0x616c6f6e/esp32s31-mp3/mechanical/connector-layout/README.md

# H1 马达 / H2 电池线束方案

打开 `Q2_Connector_Layout.FCStd`。本装配使用当前 `hardware-q2-placement` 的实际元件 STEP，结合保存的 E 版外壳，增加马达、候选托座及五根导线通道。外壳仍为 50 × 80 × 13.5 mm，主板仍为 46 × 76 mm；没有增加 PCB 走线。E 版原文件保留。

默认视图隐藏 LCD、操作小板、其螺钉和后盖，电池半透明，以便查看内部线束；可在对象树恢复显示。`connector-plan.png` 是带说明的位置图，`assembly-isometric.png` 和 `assembly-top.png` 为 FreeCAD 装配预览。

## 连接器与位置

| 位号 | 板端 / 线端 | KiCad 坐标、角度、板面 | 外壳坐标 |
| --- | --- | --- | --- |
| H1 马达 | JST BM02B-ACHSS-GAN-ETF / ACHR-02V-S | (130, 113) mm，−90°，F.Cu | (19, 64) mm |
| H2 电池 | JST BM03B-ACHSS-GAN-ETF / ACHR-03V-S | (142, 109) mm，−90°，F.Cu | (7, 60) mm |

两者均为 1.2 mm 间距、顶部插合、侧面出线的 ACH 端子，标称插合高度 1.4 mm。1～3 芯规格在 AWG28 条件下额定 2 A。H1 靠近 U11 马达驱动区，线束从电池下方绕到其右侧的马达；H2 位于电池左边缘附近，通过过孔连接背面的充电/电量计电路。两座沿外壳 +X 出线，插装顺序为先插线束，再安放电池和操作小板；装好电池后不能直接向上拔插 H1。

| 接口 | 1 脚 | 2 脚 | 3 脚 |
| --- | --- | --- | --- |
| H1 | MOTOR_OUT_N | MOTOR_OUT_P | — |
| H2 | VBAT | BAT_TS | GBAT |

H1 的两根线都是差分驱动输出，不是电源正负线。H2 的 GBAT 是电池负端，经电流检测电阻接系统地，布线时不能旁路检测电阻。针序按 PCB 焊盘编号核对，不能凭预制线颜色判断；电池线束必须按本项目顺序压接。两芯/三芯壳避免接口互插。

电池线建议 AWG28、绝缘外径不超过 0.63 mm，压接端子 SACH-003G-P0.2。马达原配 AWG32 线需使用 SACH-003G-P0.2B，并核对绝缘外径在 0.38～0.50 mm 范围；不符合时应换用匹配线材/线束。线束模型只是通道，不是生产线长和折弯图。

来源：[JST ACH 官方规格](https://www.jst-mfg.com/product/pdf/eng/eACH.pdf)。KiCad 标准库提供本版焊盘封装；3D 使用项目自建的保守插合包络，不是厂商精细 CAD，生成脚本在 `../../hardware-q2-placement/scripts/build_ach_models.py`。

## 推荐马达

候选 **Precision Microdrives C08-005 圆形 LRA**，与现有 DRV2605L 驱动方式匹配。数据表修订 004 的尺寸为直径 8 ± 0.1 mm、厚度 3.3 ± 0.15 mm，额定 1.8 Vrms、235 Hz。不能把官网旧摘要中的 3.2 mm 当作最大厚度。样机需按装配质量校准 DRV2605L 的 LRA 模式和驱动电压；这是候选选型，尚未完成实物振感验证。

马达中心外壳坐标 **(39, 57) mm**，底面 Z=7.1 mm；位于电池右侧、操作小板下方，与天线和屏幕排线区域分开。按直径 8.1 × 厚度 3.45 mm 最大包络检查，与操作小板间隙 0.55 mm，与电池预留包络间隙 2.65 mm。侧壁托座为候选结构，内径 8.3 mm、外径 9.2 mm，底板 Z=6.7～7.0 mm，预留 0.1 mm 胶层和出线槽；强度、材料、加工公差待打样。托座与外壳侧壁的接触是设计连接。

来源：[C08-005 官方数据表](https://www.precisionmicrodrives.com/datasheets/C08-005%20-%20datasheet-004.pdf)。该数据表标为采样目标规格，采购前向厂商确认供货版本。

## 电池建议与选型边界

推荐方向是 **单节 3.7 V、4.2 V 满充的高倍率软包，带保护板和独立 NTC 引线**。优先向厂商询价 252030 / 302030 尺寸级的定制成品包；型号数字只是电芯尺寸线索，不能作为成品装配尺寸承诺。当前未找到同时有可核实尺寸、电流和三线定义的现成型号，因此没有在 BOM 中虚填具体电池料号或容量。

现有电池预留空间为外壳 (8.3, 37, 7.8) mm 起的 **24 × 34 × 3 mm** 包络。建议向电池厂提出以下采购目标：

- 成品包平面最大 22 × 32 mm，含保护板、胶带和极耳折边；让厂家给出初始厚度、循环后最大厚度及膨胀余量，确认都能被现有高度空间接受。必要时重新调整内部叠层，不能强压软包。
- 初步电流筛选目标为持续至少 0.6 A、脉冲至少 1 A / 100 ms；这些是待整机测量校核的需求目标，不是已经验证的电池性能或整机功耗。容量按厂商可实现方案确认。
- 线从电池上短边靠左处引出，三线按 H2 针序压接；电池负端与 NTC 公共端的连接方式必须与电路匹配。
- NTC 优先按现有 BQ25895 的温度检测网络匹配，不能只看“10 kΩ”就认定可互换；核对 B 值、温度曲线及保护阈值。当前 R10 标为 `0R/NC`，需在确定电池后明确装配为 0 Ω，并结合 R13=5.23 kΩ、R14=30.1 kΩ 校核；本次没有宣称温度保护已经验证。
- 确定电池后再设置 BQ25895 充电电流、终止电流和充电电压，不能直接沿用大容量电池的参数。

例如 [Honcell HCP302030NZC 150 mAh 成品数据表](https://www.honcell.com/Public/Uploads/uploadfile/files/20240409/DATASHEETHCP302030NZC3.7V150mAhPACK2024EDRE01.pdf)给出的持续放电电流仅 150 mA，不满足上述初步筛选目标，所以本方案没有把它作为可直接采购的推荐件。

## 检查与使用

`fit-check.json` 记录新增马达最大包络、托座、导线与 122 个元件以及外壳/电池/操作小板/排线的实体相交检查。排线插接、线材最小弯曲半径、装配工具空间、电池寿命膨胀和完整公差链尚未验证。

KiCad 当前 DRC 0 违规、0 原理图一致性问题，386 条未连接符合未布线状态。原 555 个焊盘的身份及网络保留，新增 4 个无网络机械固定焊盘。原理图仅修改 H1/H2 的值、封装、资料和供应商字段；连接器图形仍使用原通用针脚图形以保持所有接线位置不变。

`../../hardware-q2-placement/scripts/build_harness_assembly.py` 可由 FreeCAD 重建本规划装配；将覆盖本目录生成结果，不会改写 E 版外壳。该文件是布局与结构讨论模型，尚不是可直接投产的外壳或线束图纸。
