0x616c6f6e/esp32s31-mp3/mechanical/enclosure-q2/README.md

# Q2 外观修订 B 与 2.09 英寸屏幕模型

本版取代旧 A 版作为外观方向：采用 Q2 的大圆角机身、上部横向圆角黑色屏窗、下部黑色操作环和中心电源键，正面不露螺丝。旧 `../enclosure/` 保留用于追溯。**本版是外观和屏幕结构原型，现有 KiCad PCB 尚不能直接装入，不能作为整机生产定版。**

## 打开文件

- `ESP32S31_MP3_Q2_B.FCStd`：原生 FreeCAD 外壳工程，`Parameters` 表驱动盒体、开孔、屏幕和操作环的原生布尔特征。默认显示整机外观。
- `LCD209_36x43.FCStd`：独立屏幕工程，包含背光外形、LCD 玻璃、显示区、展开排线和 21 个端部触点。
- `exports/q2-front.png`、`q2-assembled.png`、`q2-exploded.png`：正面、立体和爆炸图。
- `exports/lcd-dimensions.svg` / `.png`：屏幕尺寸图；`lcd209-flat-reference.step` 为带展开排线的模型，`lcd209-module-only.step` 为模组外形。
- `exports/q2-*.step` / `.stl`：外壳、后盖、操作环面片和中心键四个样件。STL 仅供外观/结构打样，不代表装机兼容。树脂材料和收缩补偿仍须按打印工艺选择；1.2 mm 壁厚不是已验证的 FDM 工艺规格。
- `exports/pcb-target-envelope-NOT-ROUTED.step`：47 × 76、R10.5 的新 PCB 轮廓建议实体，**不是新 KiCad 布线文件**。

## 外观和尺寸

主体为 50 × 80 × 13.5 mm，另加屏幕保护盖板后最大厚度 14.2 mm，与所查 Q2 标称外包络一致。主体平面 R12、边缘滚圆 0.55、盖板 46 × 40 × 0.6 / R10.5、操作环直径 33、中心键直径 11.4 mm 均为依据实物照片比例拟合的设计值，不是厂家机械图数据，不能声称精确复刻。

官方说明书第 12 页确认：中心键控制电源/亮灭屏；上方返回，左右切歌，下方播放暂停；圆环为音量触摸环。本版保留该外观与预留空间。当前主板没有完整的操作环电路，需另外设计电容感应环和按键板；中心开关可按既有设计需求连接 KEY/GND，但开关型号、行程、固定方式尚待选型。黑色环面片应采用可透电容感应的非金属材料。

本项目现有硬件只有 3.5 mm 耳机口和 USB-C，不包含 Q2 的 4.4 mm 平衡口；开孔按现有电路接口数量设计。TF 开孔也按现有卡座位置布置，因此接口布局不是 Q2 的逐孔复制。后盖两颗 M1.6 螺钉从背面装入，1.3 mm 导孔与头部空间为打样设计值。

## 屏幕尺寸的依据

| 项目 | 用户图纸 / 本版采用值 |
|---|---|
| BL 外形 | 36.33 ±0.1 × 43.45 ±0.1 mm |
| LCM 总厚 | 1.46 ±0.1 mm |
| LCD 玻璃 | 36.13 × 43.25 mm |
| A.A. 显示区 | 34.18 × 40.05 mm，顶部内缩 1.05 mm |
| 安装方向 | 模组旋转 90°，43.45 横向、36.33 纵向 |
| FPC 从模组边缘展开长度 | 46.14 ±0.5 mm |
| FPC 尾宽 / 触点中心跨度 | 6.6 ±0.05 / 6 ±0.03 mm |
| 间距 / 露铜长度 | 0.3 ±0.03 / 2.5 ±0.3 mm |
| 显示规格 | 2.09 英寸 IPS，320 RGB × 375，QSPI，驱动 IC 9855 |
| 触摸层 | 资料标注“无”，模型不将其视为触摸模组 |
| 资料连接器 | OK-F302-21115，与 PCB 现有封装尚未核对兼容性 |

图纸右侧 A.A. 内缩 1.08 mm 与按名义宽度居中得到的 1.075 mm 存在 0.005 mm 四舍五入差。本版以 A.A. 宽度和居中为准，不把该差异误作公差。

**估算项**：模组 R10、A.A. R9；FPC 宽颈 18 × 12.8、膜厚 0.12、折弯中性层 R0.8、触点宽 0.18 / 铜厚 0.015 mm。宽颈的实际过渡曲线、补强片、触点面朝向和引脚 1 方向未获得完整标注。玻璃/背光厚度拆分 0.30/1.16 只作示意，保证模组总厚 1.46。图示黑色单面胶 0.03 mm 是否已计入 LCM 总厚待供应商确认，未擅自把总厚增加至 1.49。

外加保护盖板和 0.18 mm 周边胶框是本设计的额外部件，不是用户屏幕资料中的 TP。排线折叠模型保持 46.14 mm 的中性线长度，含半圆弯折长度 πR；它是空间研究，不是经过供应商批准的弯折方案。折叠端部位于机身坐标 x≈3.10 mm，**未与原 FPC2 实际插接**。折弯模型是几何快照，修改 FPC 参数后须重新构建。

## 现有 PCB 的实际冲突

检查用的是当前 KiCad 导出的板体及 A 版器件包络，板体位置 x=1、y=1、名义后铜面 z=7.1 mm；坐标 +Y 朝底部接口，+Z 朝屏幕。器件 XY 来自封装，器件高度仍是估算。

- 现有 48 × 76 / R1.2 PCB 与大圆角壳体相交体积 **90.001504 mm³**。需要修改板角、边缘布局及固定孔，不能靠扩大壳体解决后继续称为 Q2 尺寸。
- 保守器件包络检查涉及 **U9、H1、C5、C58、CN1**。详见 `exports/validation.json`；U9 和 H1 为主要相交项。现有 PCB 和器件的相交实体已存为红色可视对象，预览为 `pcb-conflict-review.png`。
- 屏幕移到上方后，金属背光区域在 XY 上覆盖现有 U9 天线区域。需重新安排主控/天线与屏幕的位置，不能把三维不碰撞等同于射频合格。
- FPC2 连接器、操作环感应板、中心开关、电池与新固定结构尚须联合调整。新壳的螺钉柱也可能占用原板区域；新的板框建议仅作为空间约束，未完成网络重布线。

## 验证与再生成

`exports/validation.json` 记录零件实体有效性、外包络、已建模外壳/屏幕/排线间的几何相交量，以及旧板冲突。`external_geometry_pass=true` 只表示所列外形零件检查通过；**`pcb_fits=false`** 明确表示当前 PCB 不适配。

`exports/export-verification.json` 记录四个样件 STEP 重导入为有效单实体、STL 封闭、屏幕 STEP 外形尺寸复核，以及原生参数改变后重算/恢复。未验证真实器件公差、胶粘强度、开关寿命、防水、射频或量产装配。

参数来源是 `parameters.json`。FreeCAD 内的 `Parameters` 支持编辑原生特征；对于排线折叠、参考几何、图标和爆炸图这些快照，需要修改 JSON 后重建才同步。运行 `Rebuild.FCMacro` 前保存并关闭本目录的两个文档；脚本不覆盖旧 A 版和 KiCad 文件。重建会恢复 JSON 中的值，因此应把希望保留的表格修改同步回 JSON。

PCB/器件/电池参考形状已冻结在 `reference/source-*.brep`，来源哈希见 `reference/source-manifest.json`。PCB 或布局数据改变后，构建脚本会要求先刷新参考形状，避免用旧形状生成看似最新的干涉报告。尺寸 SVG/PNG 由 `draw_dimensions.py` 生成；调整 JSON 后需用安装了 Pillow 的 Python 重跑该脚本。

## 参考来源

- 用户提供屏幕图和参数表保存在 `reference/lcd-dimensions.png`、`lcd-specifications.png`。
- [山灵 Q2 官方说明书](http://openwin.shanling.com:9000/pdf/sms/Q2v1.0.pdf)，本地 `reference/Q2v1.0.pdf`，第 4 / 12 页用于操作件布局。
- [Q2 商品实物照片与尺寸规格](https://www.e-earphon.com/collections/new_item/products/778580)，核对正面上部横屏、下部圆环和整机 80 × 50 × 13.5 / 含屏 14.2 mm。照片仅作观察参考，未作为项目素材复制。
