0x616c6f6e/esp32s31-mp3/hardware-controls/mechanical/controls-and-keycaps.png

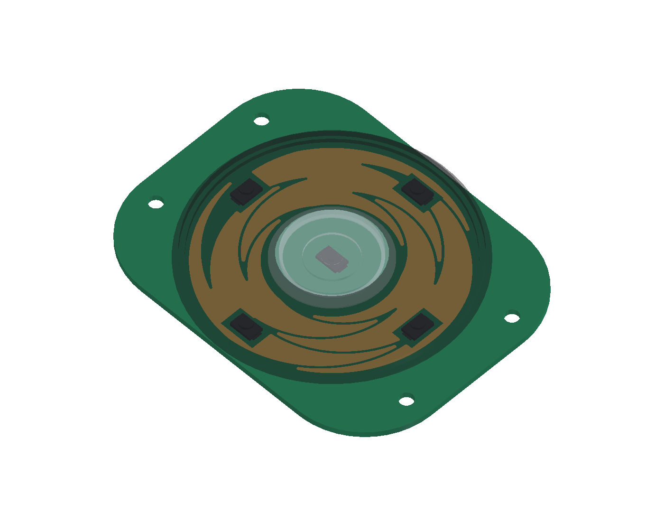
hardware-controls/mechanical/controls-and-keycaps.png
