0x616c6f6e/esp32s31-mp3/hardware-controls/mechanical/exterior.png

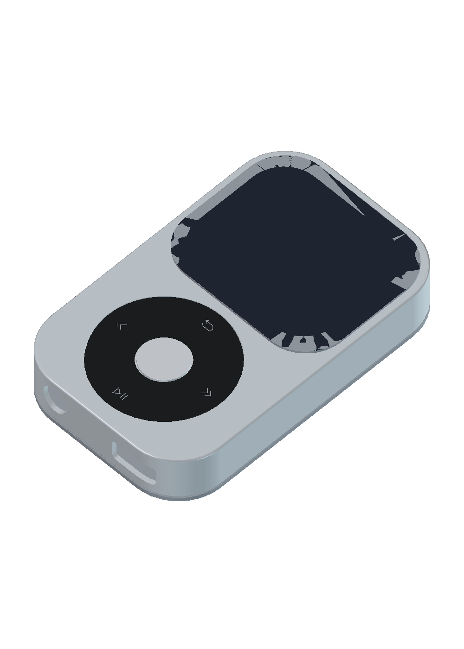
hardware-controls/mechanical/exterior.png
