0x616c6f6e/esp32s31-mp3/hardware-controls/mechanical/ffc-section.png

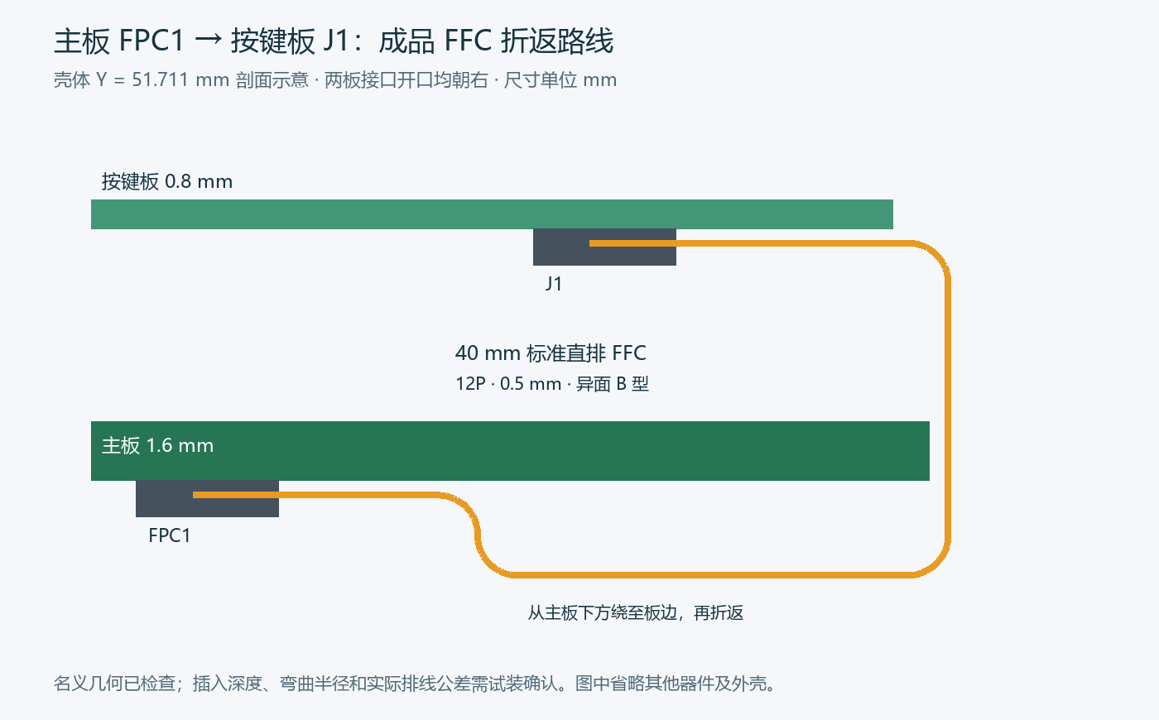
hardware-controls/mechanical/ffc-section.png
