0x616c6f6e/esp32s31-mp3/hardware-controls/output/3d-back.png

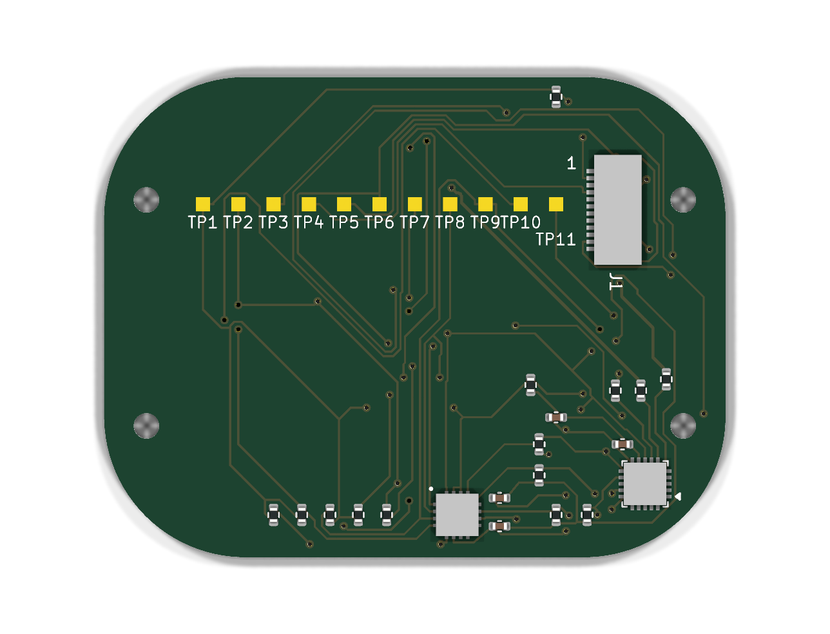
hardware-controls/output/3d-back.png
