0x616c6f6e/esp32s31-mp3/hardware-controls/output/ch32v006-review/back.png

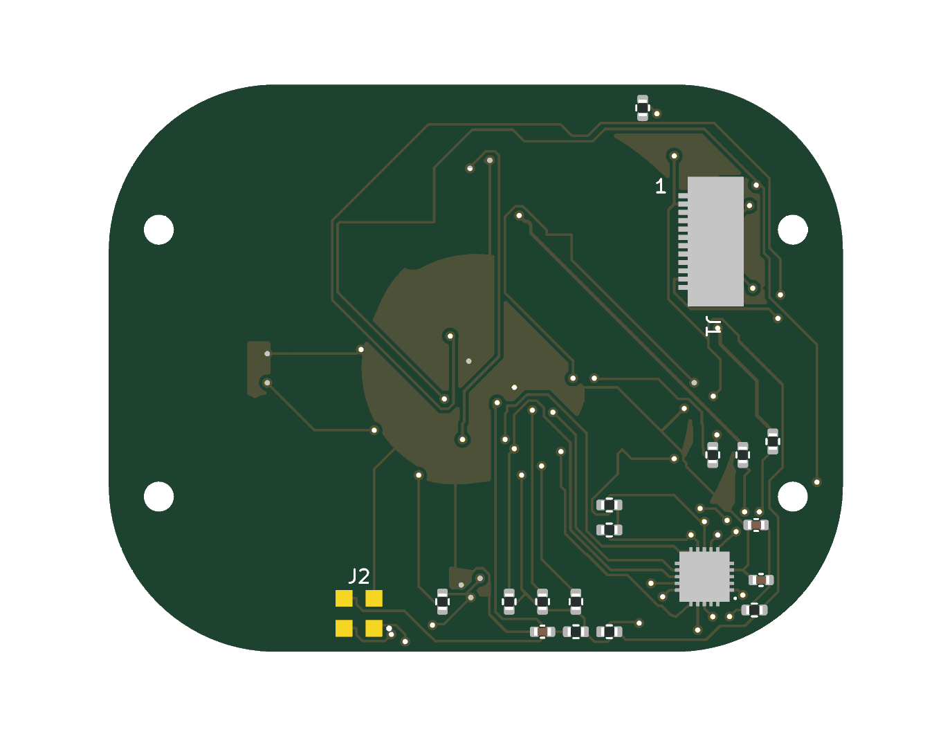
hardware-controls/output/ch32v006-review/back.png
