0x616c6f6e/esp32s31-mp3/hardware-controls/output/controls-overview.png

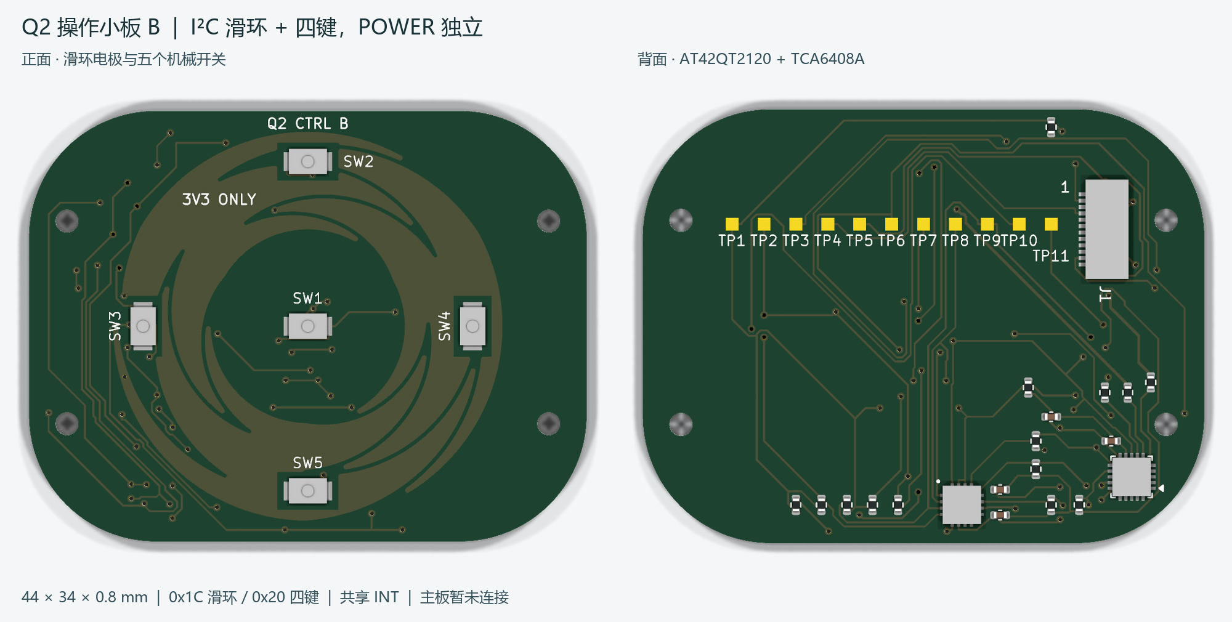
hardware-controls/output/controls-overview.png
