0x616c6f6e/esp32s31-mp3/hardware-controls/output/schematic.png

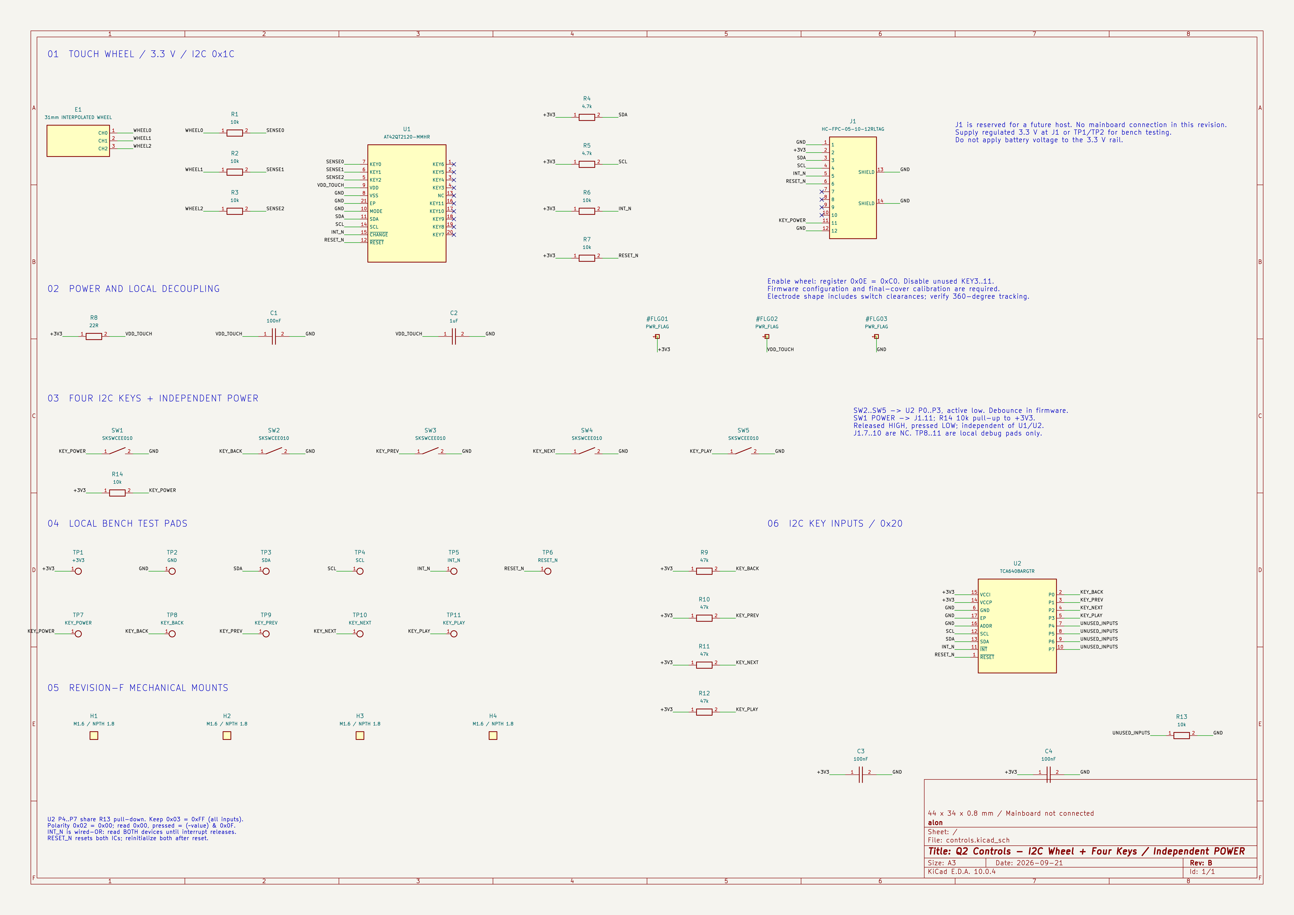
hardware-controls/output/schematic.png
