0x616c6f6e/esp32s31-mp3/hardware-display-adapter/am213-fpc-adapter/output/routing-obstacles.png

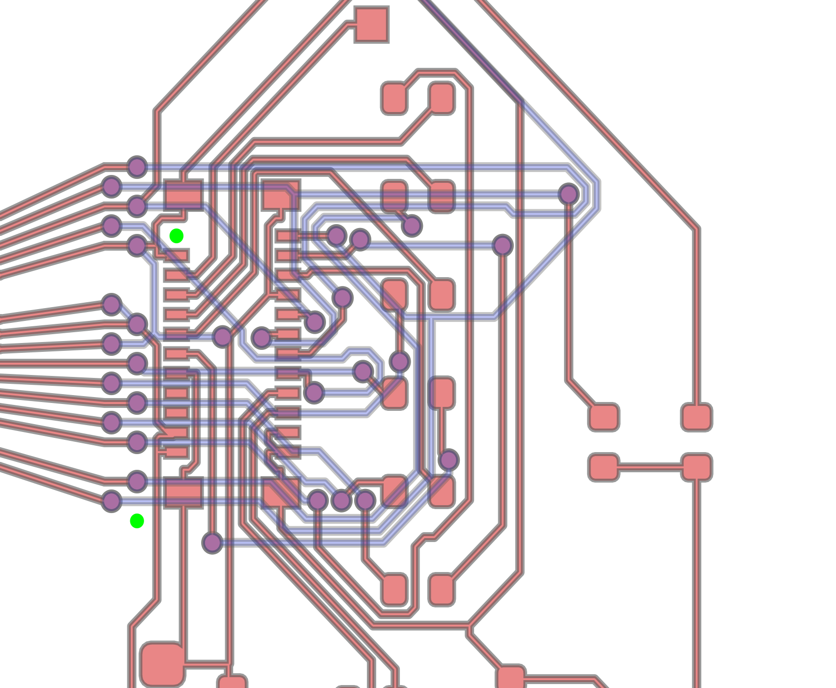
hardware-display-adapter/am213-fpc-adapter/output/routing-obstacles.png
