0x616c6f6e/esp32s31-mp3/hardware-display-adapter/am213-fpc-adapter/output/schematic/am213-fpc-adapter.png

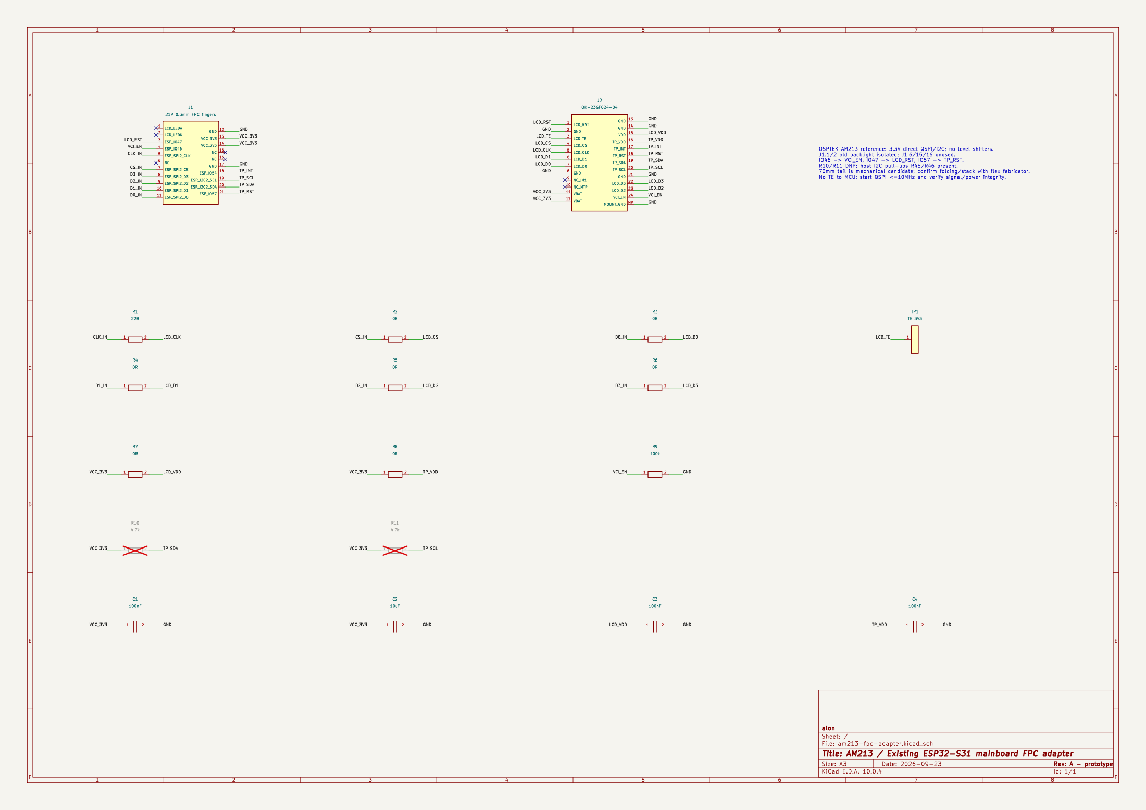
hardware-display-adapter/am213-fpc-adapter/output/schematic/am213-fpc-adapter.png
