0x616c6f6e/esp32s31-mp3/hardware-display-adapter/fpc-layout-concept.png

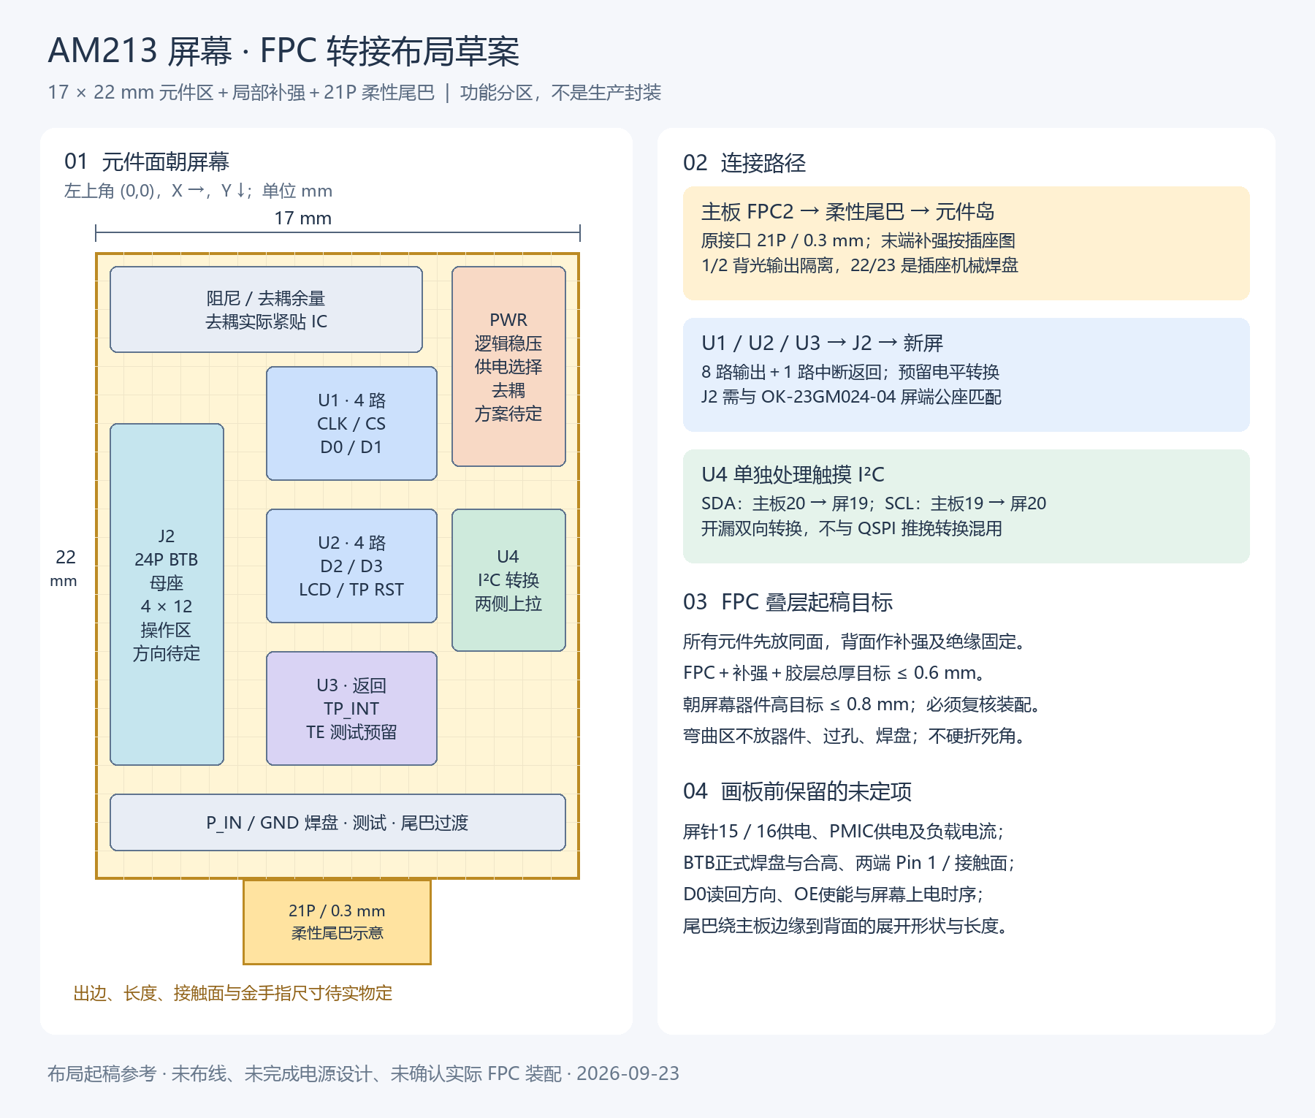
hardware-display-adapter/fpc-layout-concept.png
