0x616c6f6e/esp32s31-mp3/hardware-display-adapter/reference/1-241226143025125.png

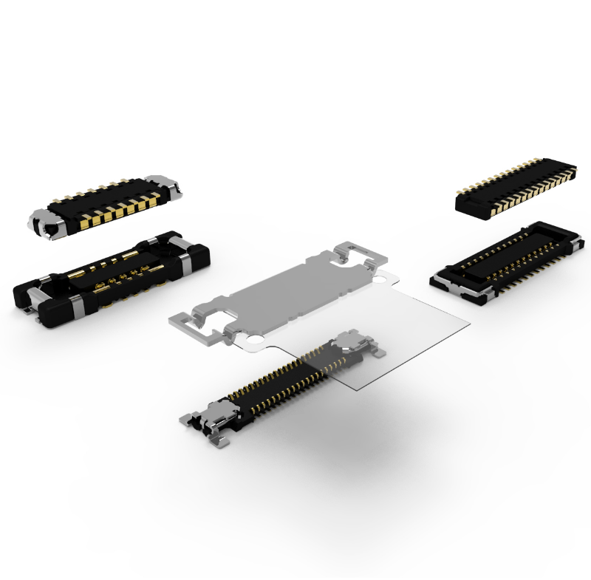
hardware-display-adapter/reference/1-241226143025125.png
