0x616c6f6e/esp32s31-mp3/hardware-q2-v2-plan/placement-overview.png

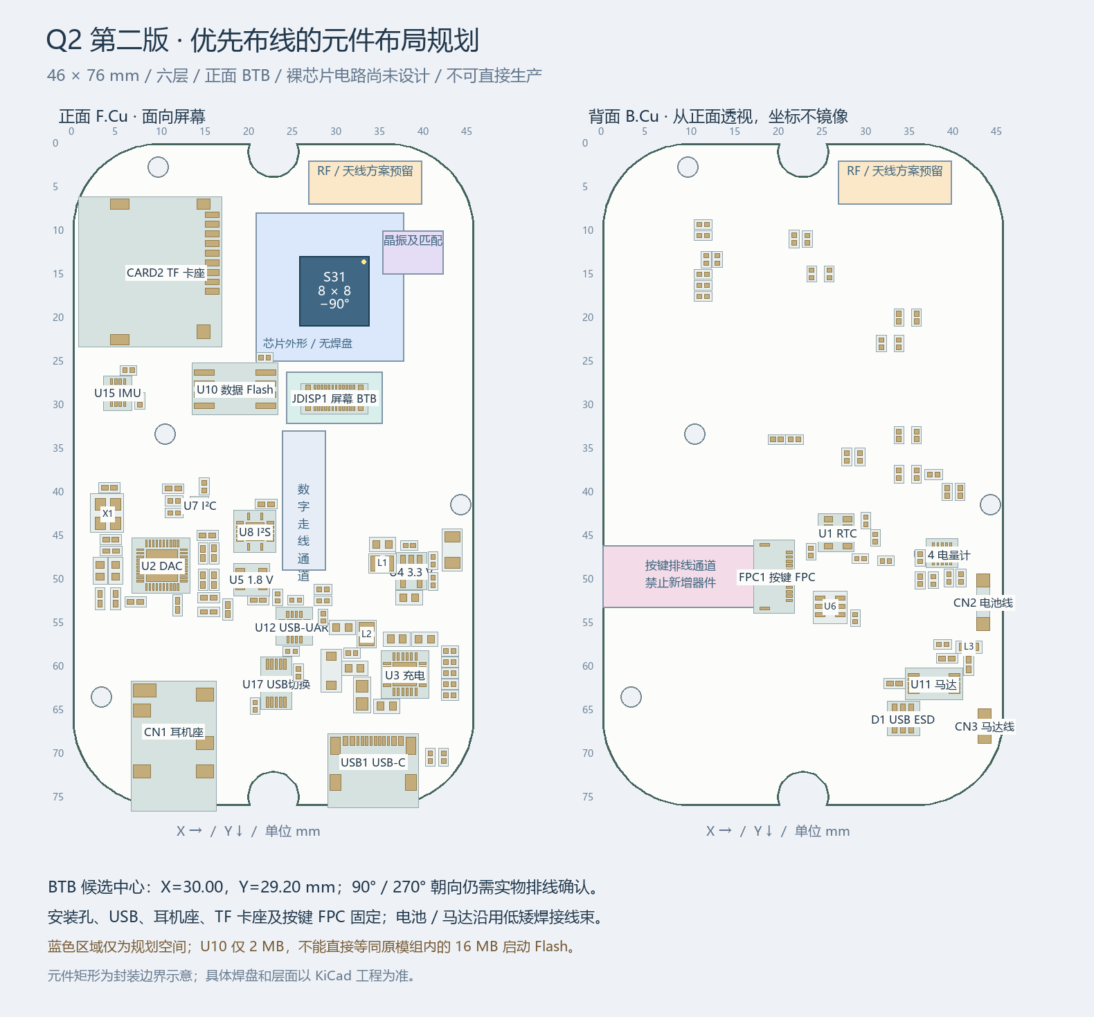
hardware-q2-v2-plan/placement-overview.png
