0x616c6f6e/esp32s31-mp3/hardware-q2-v2/output/pcb-overview.png

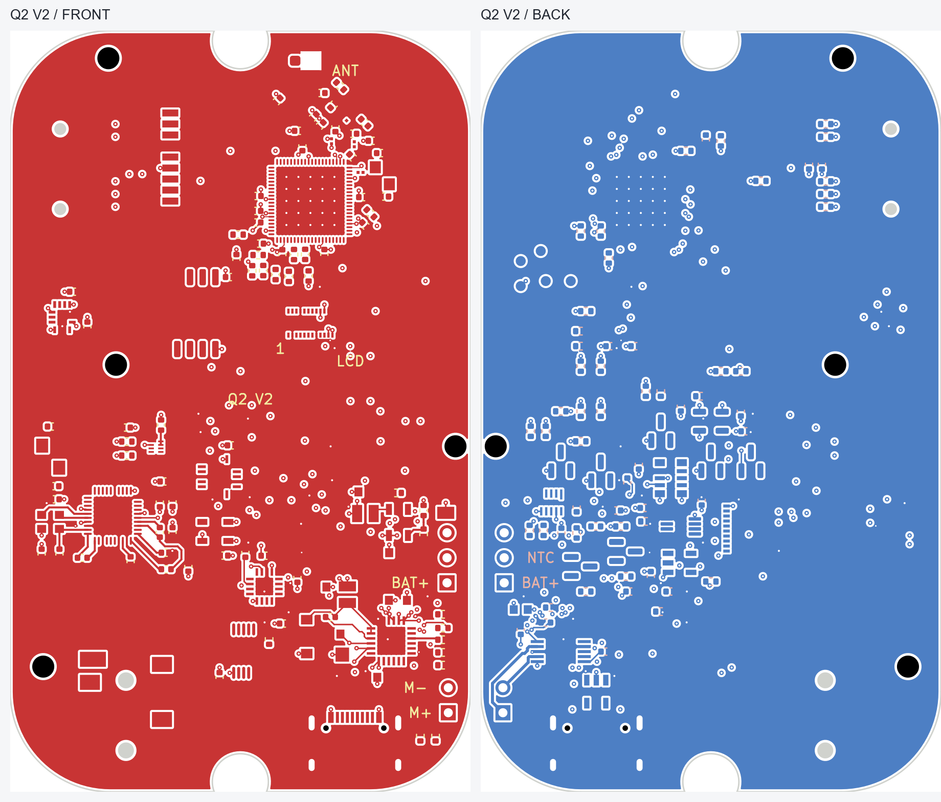
hardware-q2-v2/output/pcb-overview.png
