0x616c6f6e/esp32s31-mp3/mechanical/connector-layout/connector-plan.png

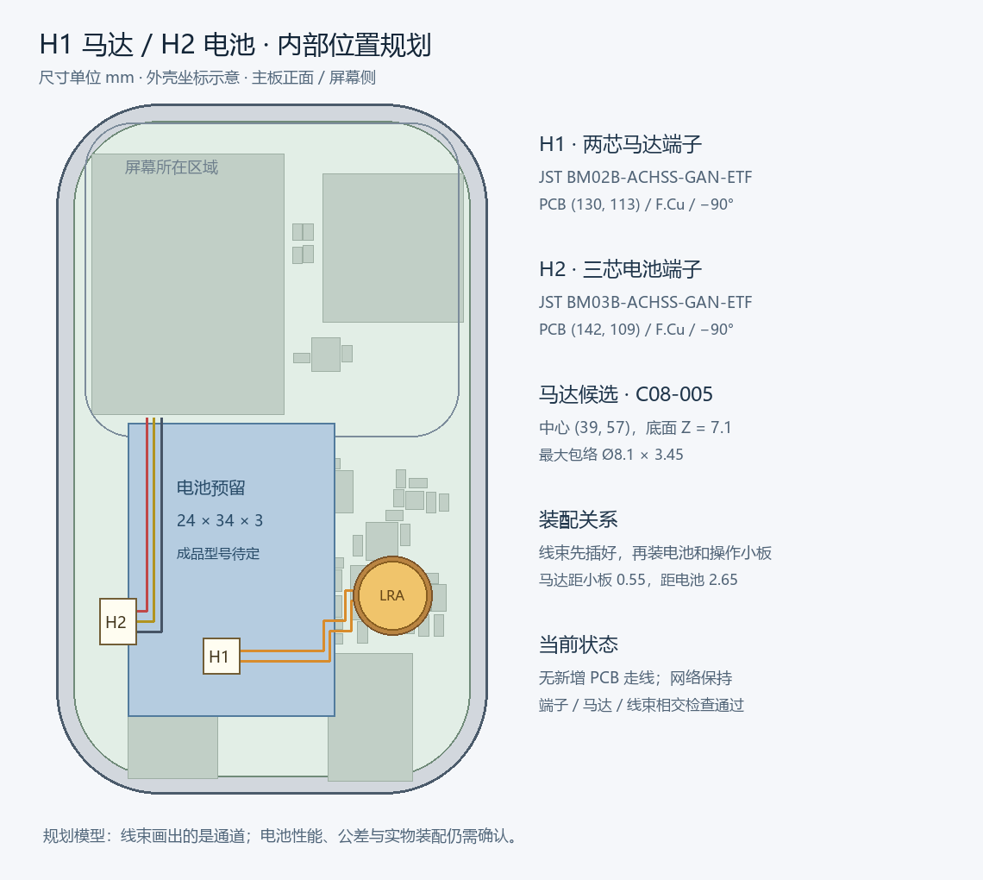
mechanical/connector-layout/connector-plan.png
