0x616c6f6e/esp32s31-mp3/mechanical/display-fit/exports/current-fit-rear-isometric.png

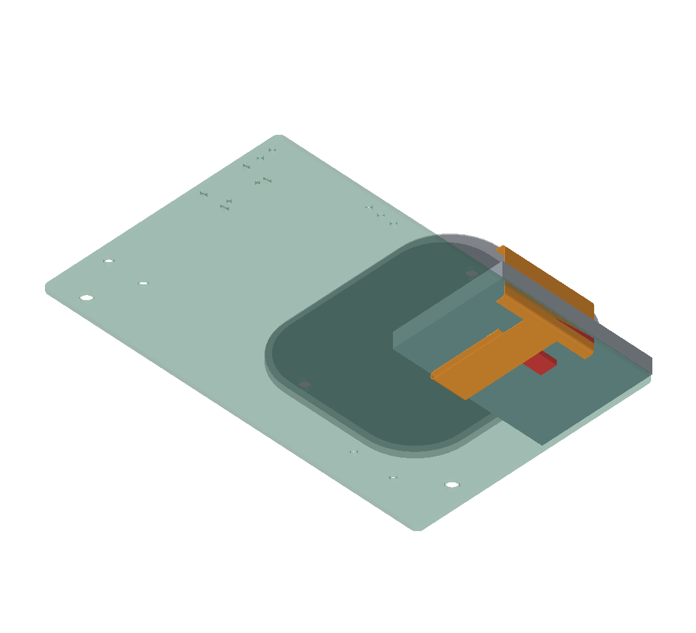
mechanical/display-fit/exports/current-fit-rear-isometric.png
