0x616c6f6e/esp32s31-mp3/mechanical/display-fit/exports/display-fit-review.png

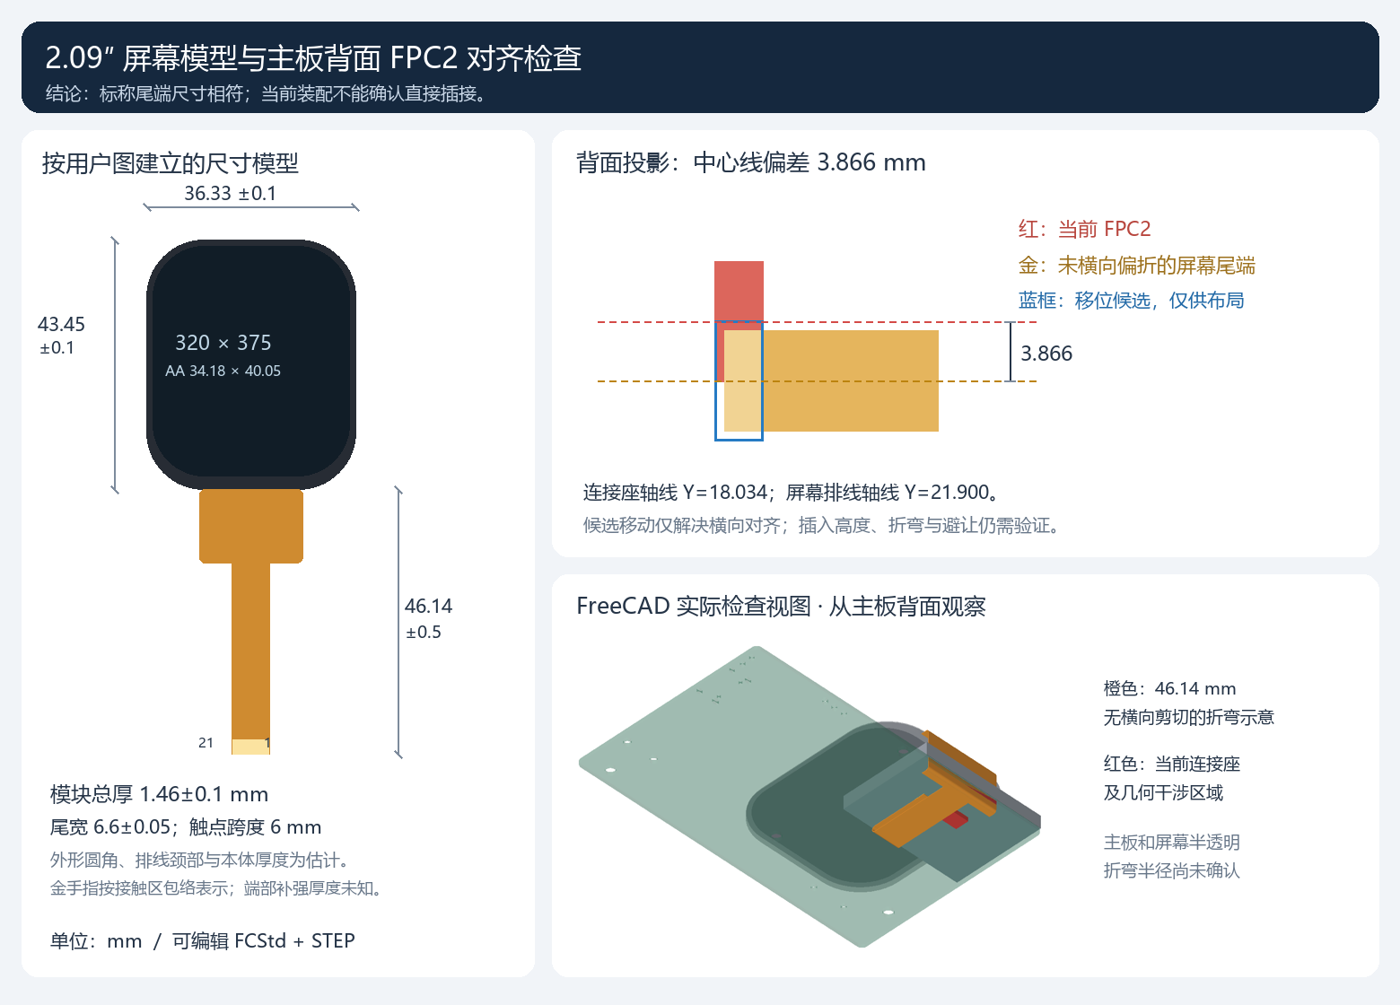
mechanical/display-fit/exports/display-fit-review.png
