0x616c6f6e/esp32s31-mp3/mechanical/display-fit/exports/lcd-native-isometric.png

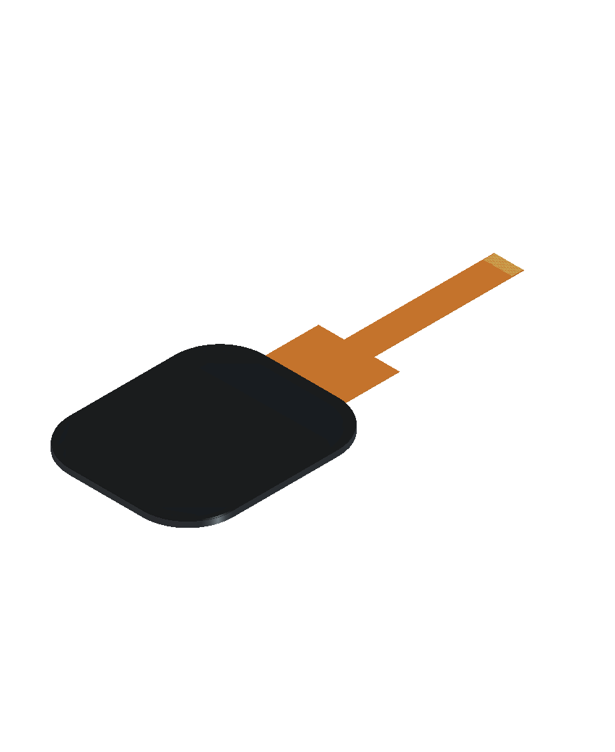
mechanical/display-fit/exports/lcd-native-isometric.png
