0x616c6f6e/esp32s31-mp3/mechanical/display-fit/reference/connector-drawing.png

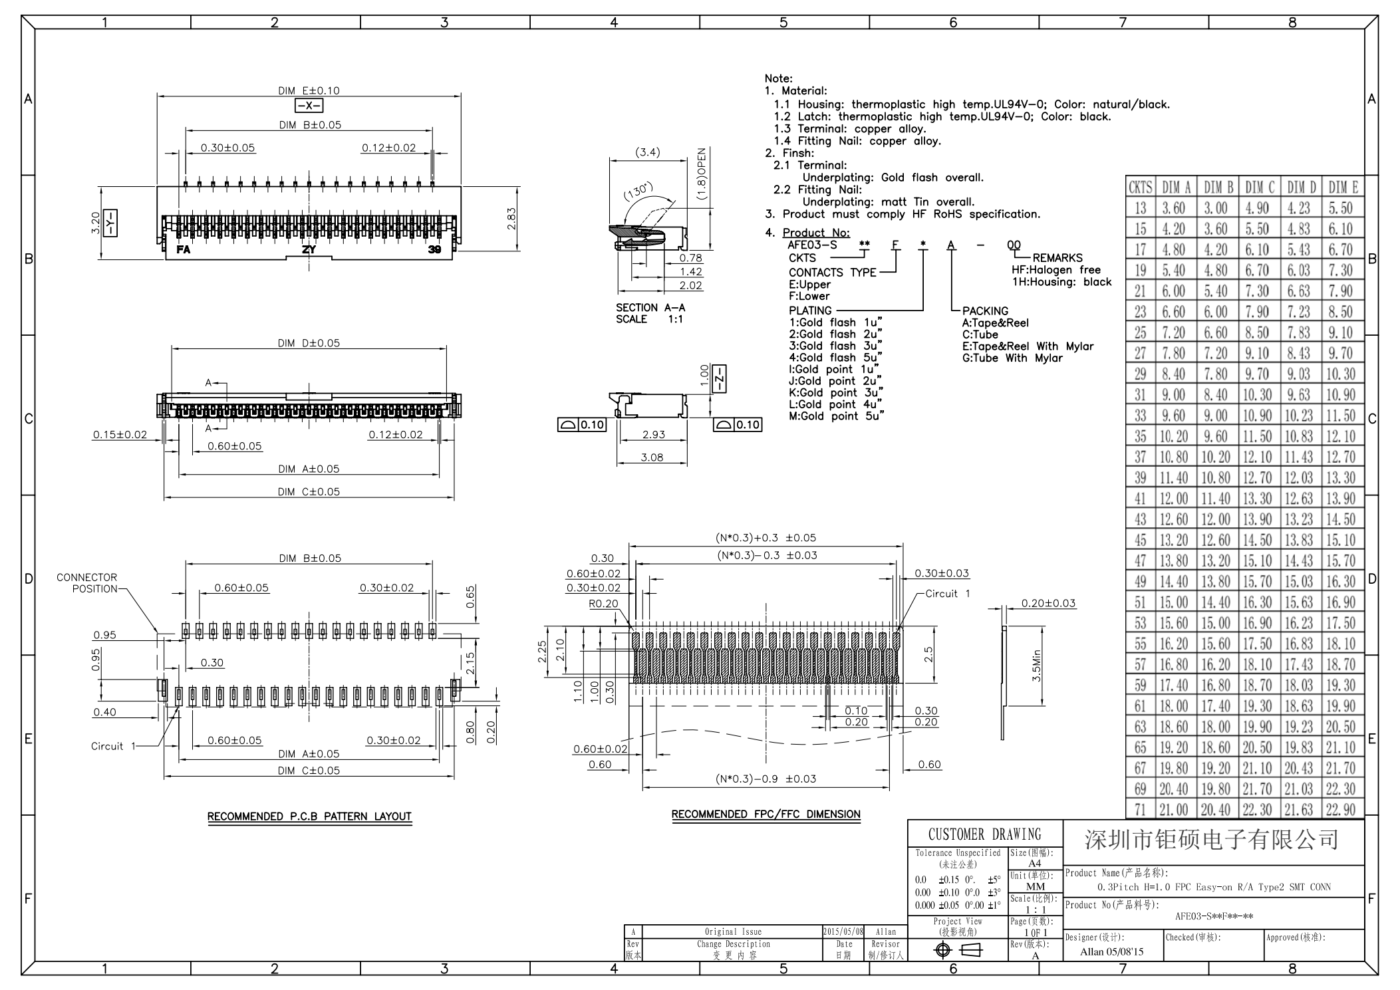
mechanical/display-fit/reference/connector-drawing.png
