0x616c6f6e/esp32s31-mp3/mechanical/display-fit/reference/lcd-specifications.png

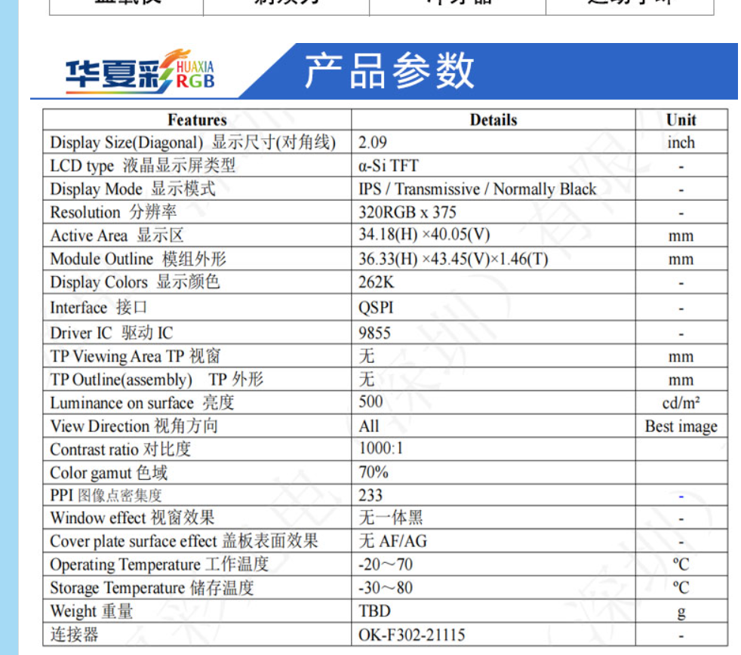
mechanical/display-fit/reference/lcd-specifications.png
