0x616c6f6e/esp32s31-mp3/mechanical/enclosure-final-g/back-internals.png

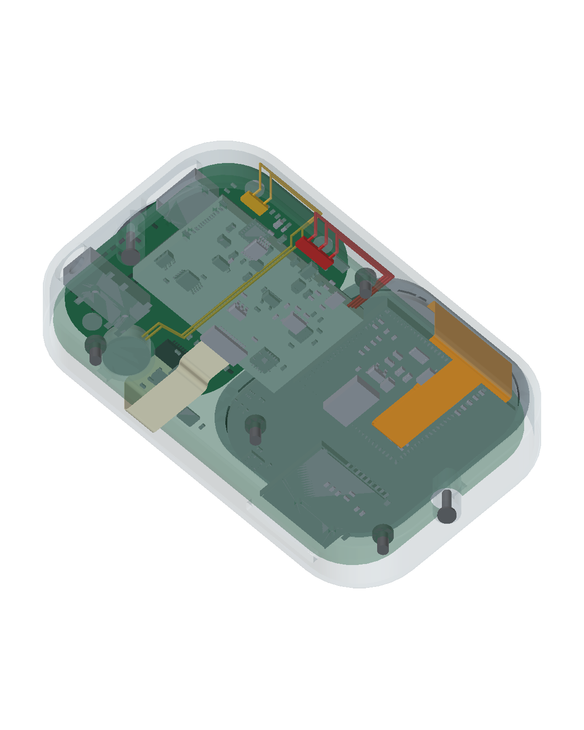
mechanical/enclosure-final-g/back-internals.png
