0x616c6f6e/esp32s31-mp3/mechanical/enclosure-final-g/reference/CN3.pdf.png

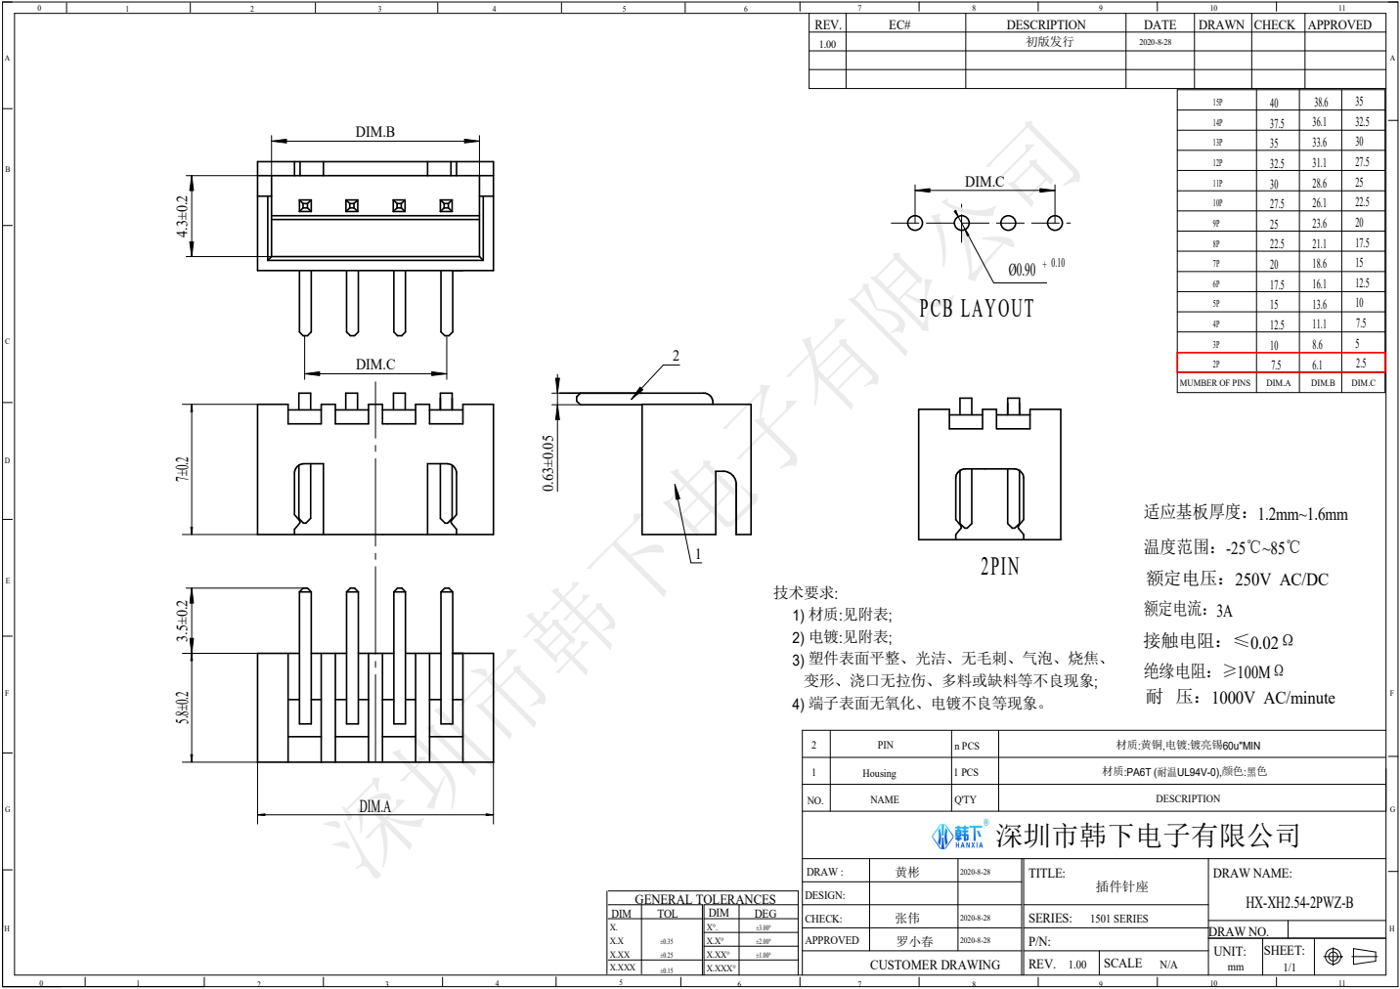
mechanical/enclosure-final-g/reference/CN3.pdf.png
