0x616c6f6e/esp32s31-mp3/mechanical/enclosure-final-h/reinforced-upper-shell.png

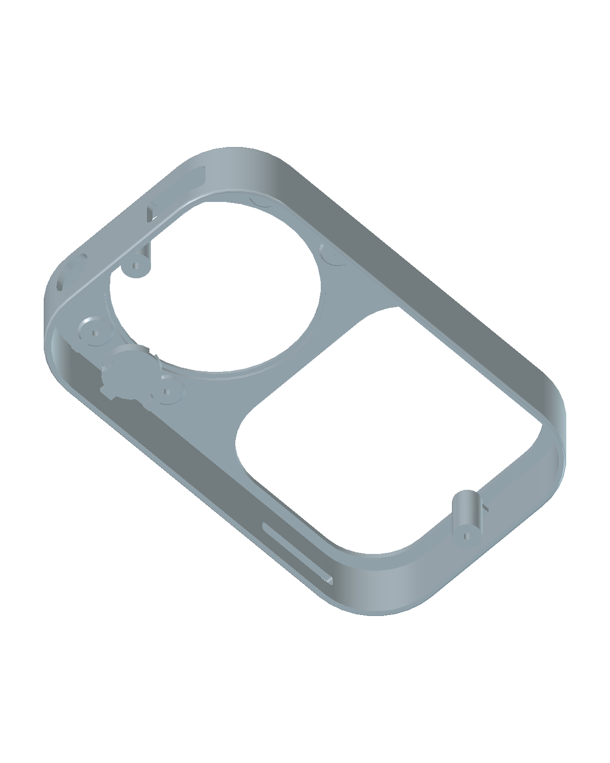
mechanical/enclosure-final-h/reinforced-upper-shell.png
