0x616c6f6e/esp32s31-mp3/mechanical/enclosure-final-j/controls-mount-view.png

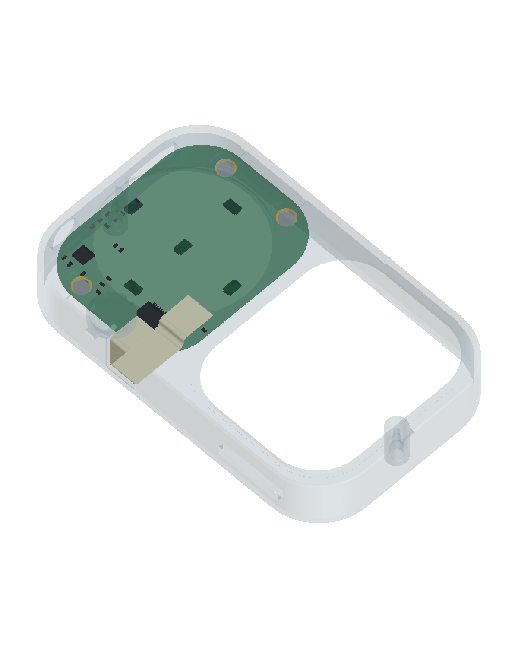
mechanical/enclosure-final-j/controls-mount-view.png
