0x616c6f6e/esp32s31-mp3/mechanical/enclosure-final-j/insert-section.png

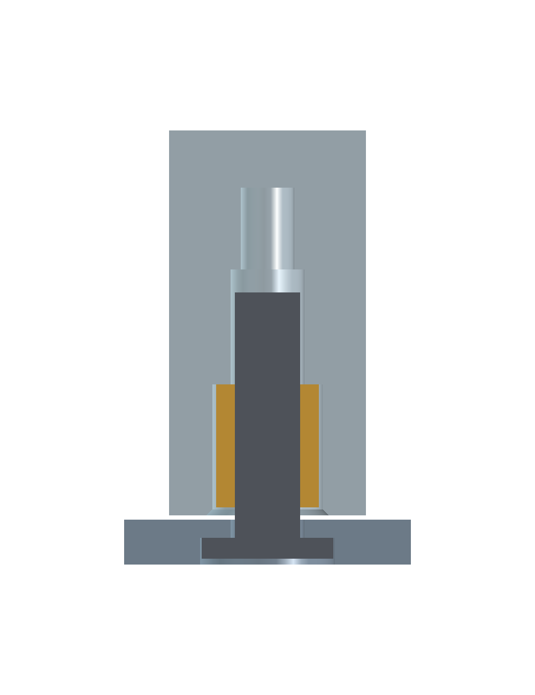
mechanical/enclosure-final-j/insert-section.png
