0x616c6f6e/esp32s31-mp3/mechanical/enclosure-q2/exports/q2-exploded.png

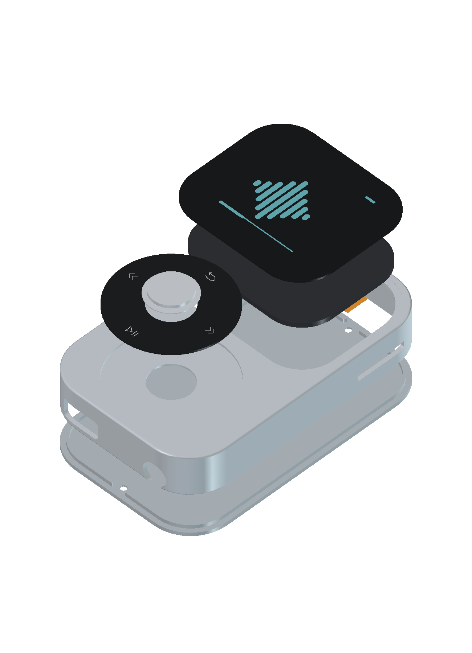
mechanical/enclosure-q2/exports/q2-exploded.png
