0x616c6f6e/esp32s31-mp3/mechanical/enclosure/exports/exploded.png

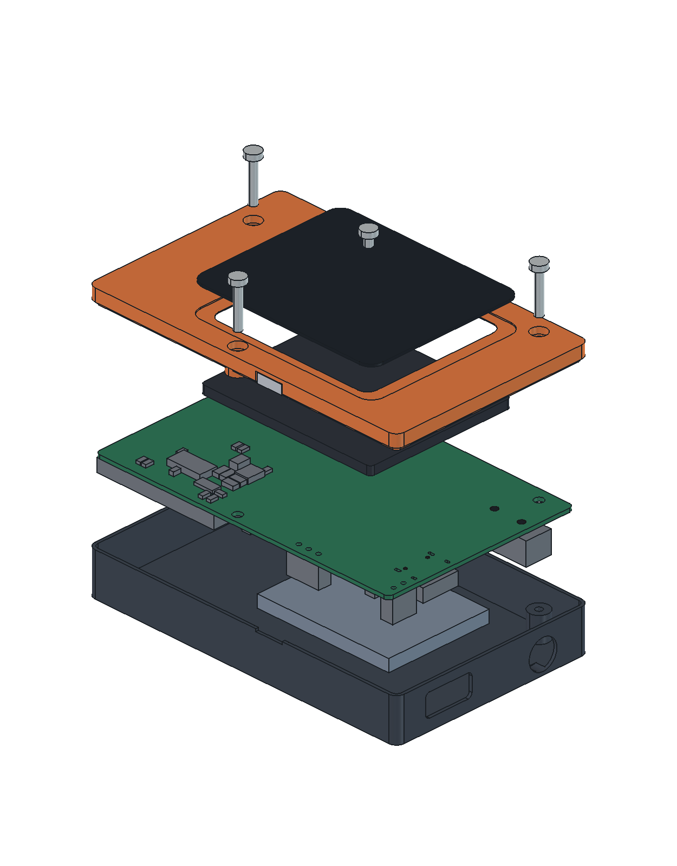
mechanical/enclosure/exports/exploded.png
