0x616c6f6e/esp32s31-mp3/mechanical/final-board-review/motor-jack-conflict.png

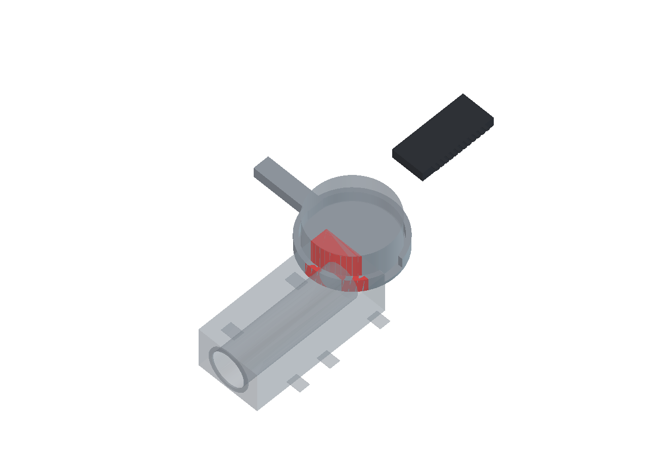
mechanical/final-board-review/motor-jack-conflict.png
