0x616c6f6e/esp32s31-mp3/mechanical/v2-btb-placement/placement-top.png

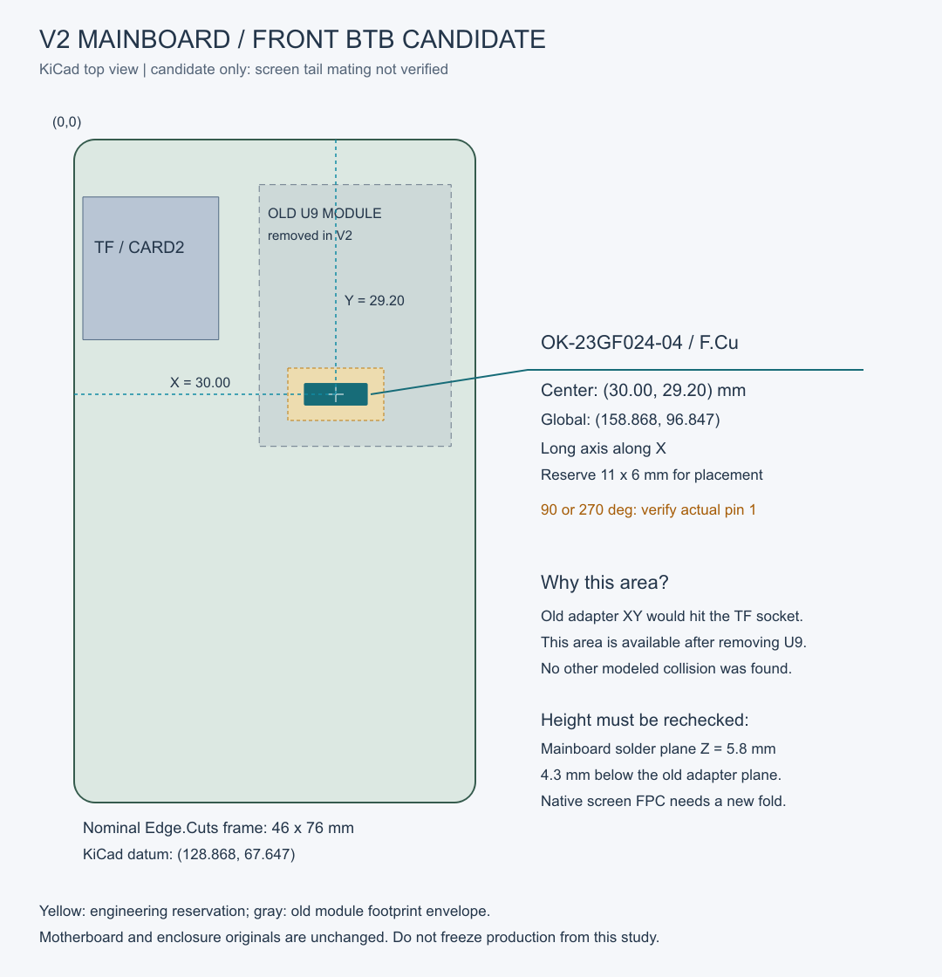
mechanical/v2-btb-placement/placement-top.png
