0x616c6f6e/esp32s31-mp3/mechanical/enclosure-q2-d/exports/mainboard-target-envelope-NOT-ROUTED.step

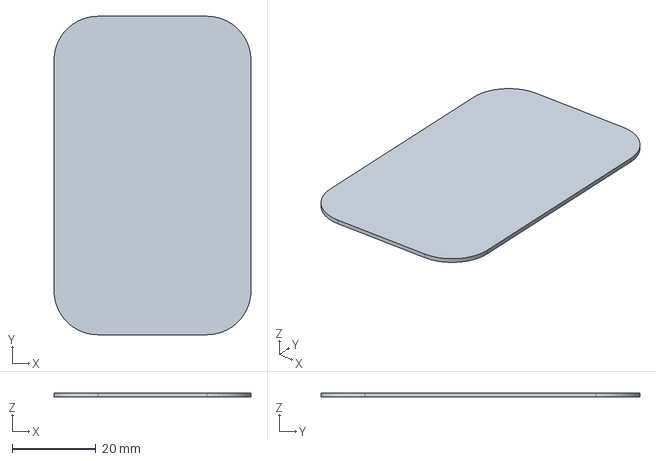
[picture p83: CAD file, 2026-09-21]
mechanical/enclosure-q2-d/exports/mainboard-target-envelope-NOT-ROUTED.step
47.0 x 76.0 x 1.00 mm
