0x616c6f6e/esp32s31-mp3/mechanical/enclosure-q2/exports/q2-appearance-assembly.step

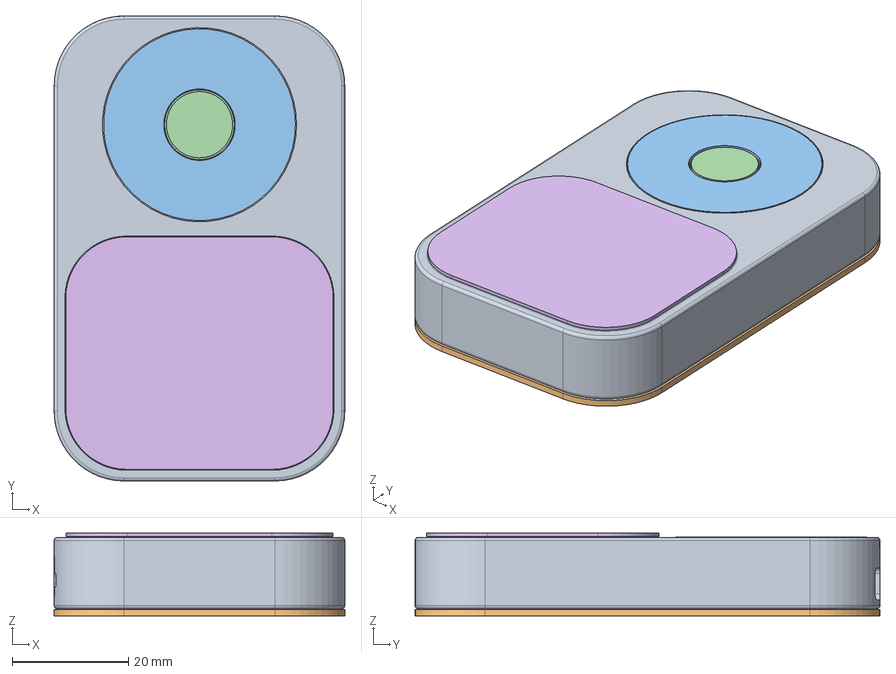
[picture p84: CAD file, 2026-09-21]
mechanical/enclosure-q2/exports/q2-appearance-assembly.step
50.0 x 80.0 x 14.2 mm
