0x616c6f6e/esp32s31-mp3/mechanical/enclosure-q2-f/exports/assembly-F-current-PCB.step

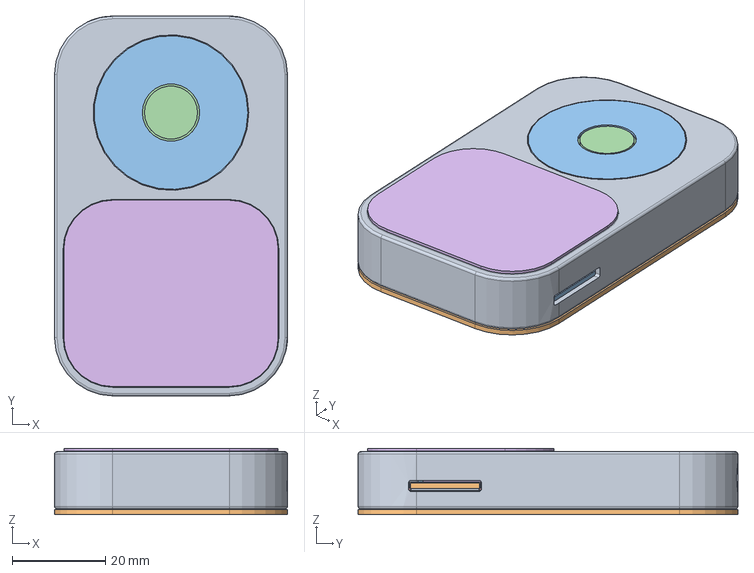
[picture p85: CAD file, 2026-09-21]
mechanical/enclosure-q2-f/exports/assembly-F-current-PCB.step
50.0 x 81.5 x 14.2 mm
