0x616c6f6e/esp32s31-mp3/hardware-controls/models3d/FH19C_12.step

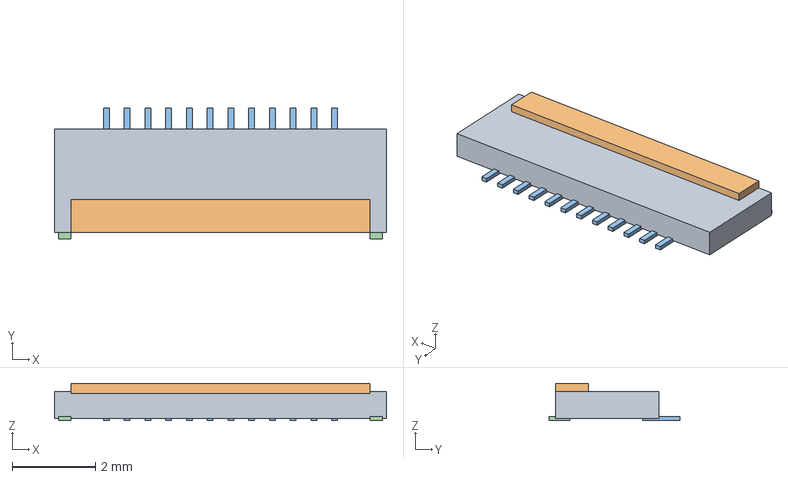
[picture p86: CAD file, 2026-09-24]
hardware-controls/models3d/FH19C_12.step
8.00 x 3.15 x 0.9 mm
FH19C_12_0
FH19C_12_1
FH19C_12_2
FH19C_12_3
FH19C_12_4
FH19C_12_5
FH19C_12_6
FH19C_12_7
FH19C_12_8
FH19C_12_9
FH19C_12_10
FH19C_12_11
FH19C_12_12
FH19C_12_13
FH19C_12_14
FH19C_12_15
