0x616c6f6e/esp32s31-mp3/hardware-controls/output/ch32v006-review/candidate/models3d/CH32V006_QFN20.step

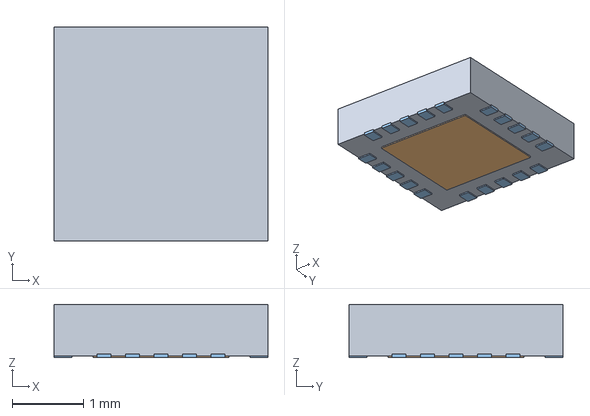
[picture p87: CAD file, 2026-09-24]
hardware-controls/output/ch32v006-review/candidate/models3d/CH32V006_QFN20.step
3.00 x 3.00 x 0.75 mm
