0x616c6f6e/esp32s31-mp3/hardware-controls/output/controls-ch32v006.step

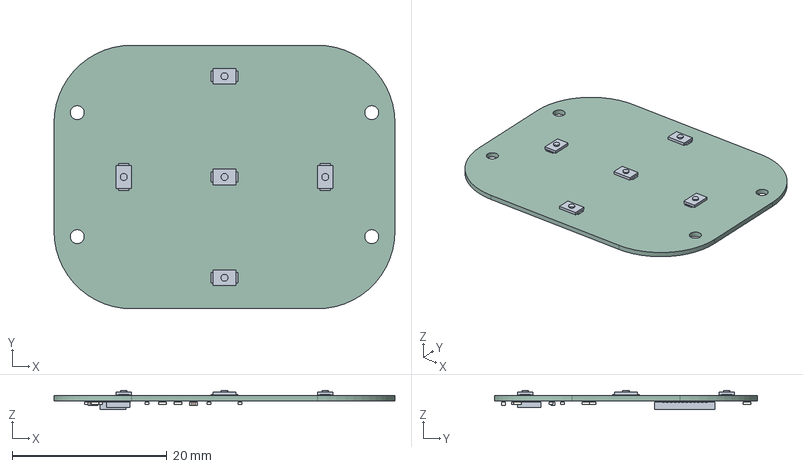
[picture p88: CAD file, 2026-09-24]
hardware-controls/output/controls-ch32v006.step
44.0 x 34.0 x 2.48 mm
SKSW_3x2_0 x 5
SKSW_3x2_1 x 5
SKSW_3x2_2 x 5
SKSW_3x2_3 x 5
C_0402_1005Metric x 3
R_0402_1005Metric x 13
Housing
Latch
Pin1
Pin2
Pin3
Pin4
Pin5
Pin6
Pin7
Pin8
Pin9
Pin10
Pin11
Pin12
Mount
Mount001
controls_PCB
