0x616c6f6e/esp32s31-mp3/hardware-display-adapter/am213-fpc-adapter/models3d/Q2_L_BTB_Fit_Review.FCStd

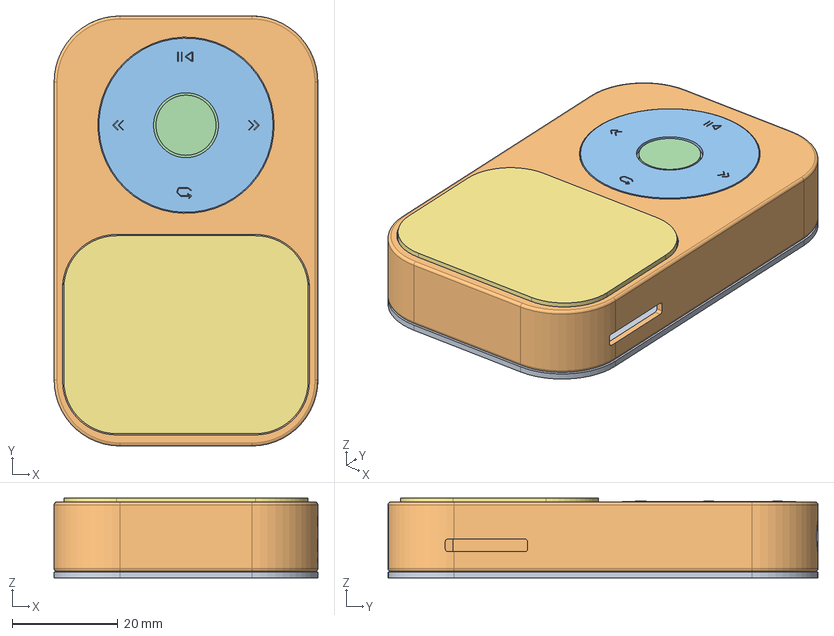
[picture p89: CAD file, 2026-09-24]
hardware-display-adapter/am213-fpc-adapter/models3d/Q2_L_BTB_Fit_Review.FCStd
50.0 x 81.5 x 15.1 mm
02 Rear cover K / 1.0 mm screw bearing seat
01 Housing L / AM213 integrated cover aperture
03 Wheel K / 1.0 mm rim / no carrier
04 Center key K / 1.0 mm rim / no carrier
USB1 / USB-C-SMD_TYPE-C-16PIN-2MD-073
CN1 / AUDIO-SMD_PJ-342B-TX-SMT
AM213 integral touch cover / 46.30 x37.50 x1.30 / NOT extra glass
ControlSymbols
2 x M1.6 x 6 / recessed heads
Housing
24 contacts / schematic, not numbered
Retention clips / simplified
Maximum dimensional envelope / not physical solid
