0x616c6f6e/esp32s31-mp3/hardware-display-adapter/am213-fpc-adapter/output/adapter-flat.step

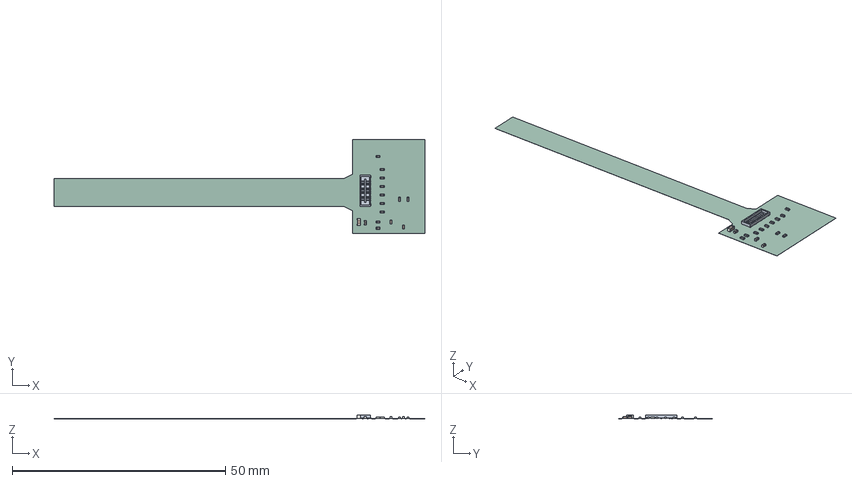
[picture p90: CAD file, 2026-09-24]
hardware-display-adapter/am213-fpc-adapter/output/adapter-flat.step
87.0 x 22.0 x 0.915 mm
C_0402_1005Metric x 3
R_0402_1005Metric x 11
C_0603_1608Metric
am213-fpc-adapter_PCB
