0x616c6f6e/esp32s31-mp3/hardware-q2-v2/models3d/ESP32-S31_QFN80_8x8.step

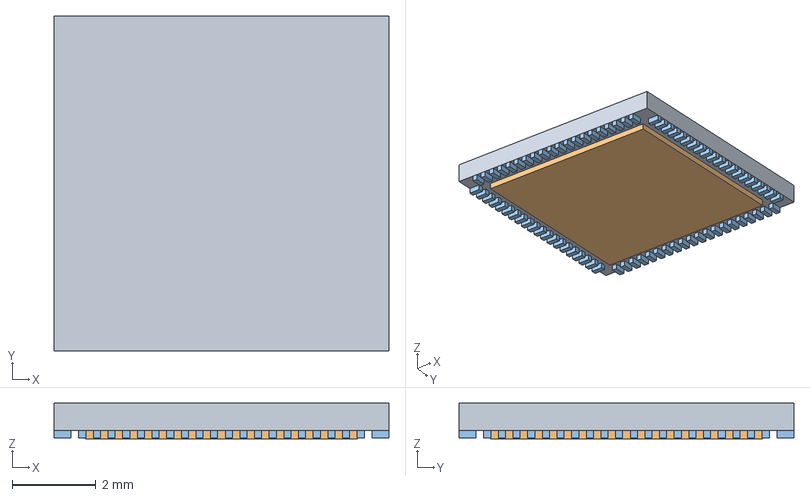
[picture p91: CAD file, 2026-09-24]
hardware-q2-v2/models3d/ESP32-S31_QFN80_8x8.step
8.00 x 8.00 x 0.85 mm
