0x616c6f6e/esp32s31-mp3/mechanical/appearance-prototype-v2/print-parts/05-screen-dummy.stl

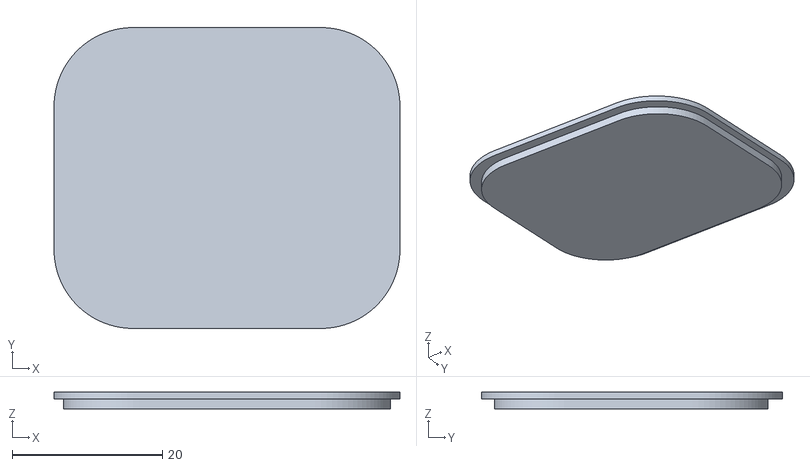
[picture p92: CAD file, 2026-09-24]
mechanical/appearance-prototype-v2/print-parts/05-screen-dummy.stl
46.0 x 40.0 x 2.20
