0x616c6f6e/esp32s31-mp3/mechanical/appearance-prototype-v2/reference/04-center-button.step

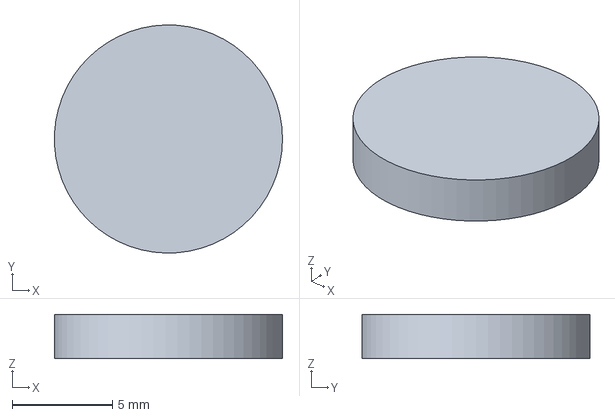
[picture p93: CAD file, 2026-09-24]
mechanical/appearance-prototype-v2/reference/04-center-button.step
11.4 x 11.4 x 2.20 mm
