0x616c6f6e/esp32s31-mp3/mechanical/connector-layout/Q2_Connector_Layout.FCStd

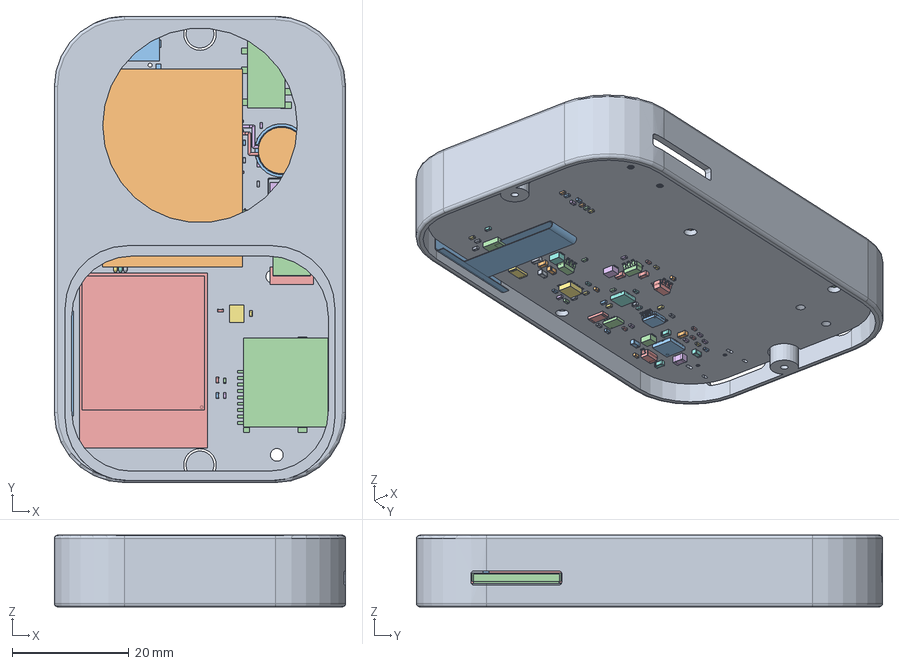
[picture p94: CAD file, 2026-09-21]
mechanical/connector-layout/Q2_Connector_Layout.FCStd
50.0 x 80.0 x 12.3 mm
HousingWithControlPosts
BatteryReference
DisplayFPCRoute
ControlFPCRoute
MainControlFPCReserve
ControlFPCConnector
PCB_U11
PCB_H2
PCB_C26
PCB_C19
PCB_R19
PCB_R29
PCB_C18
PCB_L3
PCB_C33
PCB_R26
PCB_C32
PCB_C8
PCB_R44
PCB_R30
PCB_C27
PCB_C22
PCB_C31
PCB_C20
PCB_R31
PCB_C28
PCB_USB1
PCB_U8
PCB_U9
PCB_U2
PCB_C25
PCB_C23
PCB_H1
PCB_C29
PCB_C24
PCB_C30
PCB_C5
PCB_C58
PCB_C48
PCB_C21
PCB_X1
PCB_U7
PCB_C40
PCB_CN1
PCB_C47
PCB_C41
PCB_U15
PCB_D1
PCB_U5
PCB_C34
PCB_C4
PCB_CARD2
PCB_C39
PCB_R18
PCB_C35
PCB_C17
PCB_R17
PCB_R32
PCB_U3
PCB_U16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
