0x616c6f6e/esp32s31-mp3/mechanical/display-fit/exports/lcd209-module-only.step

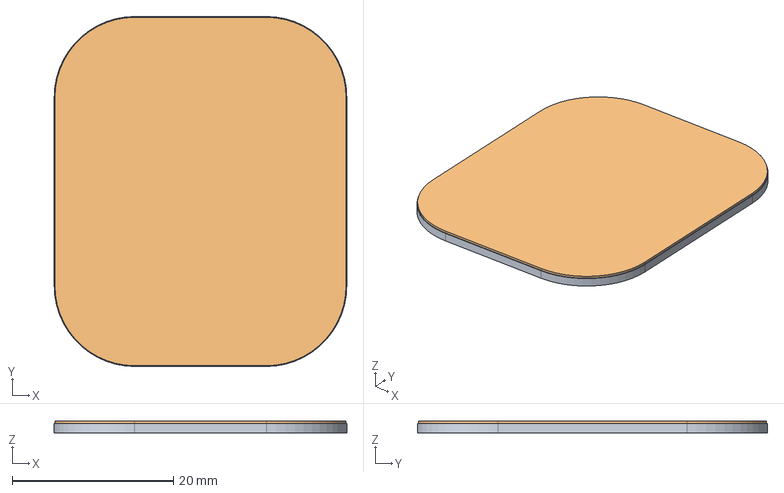
[picture p95: CAD file, 2026-09-21]
mechanical/display-fit/exports/lcd209-module-only.step
36.3 x 43.5 x 1.46 mm
