0x616c6f6e/esp32s31-mp3/mechanical/display-fit/LCD209_dimensioned.FCStd

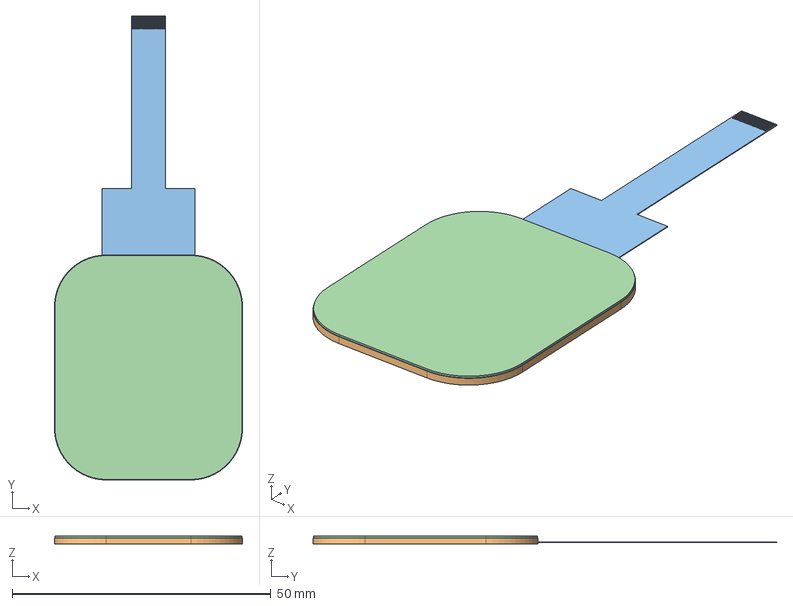
[picture p96: CAD file, 2026-09-21]
mechanical/display-fit/LCD209_dimensioned.FCStd
36.3 x 89.6 x 1.46 mm
Active area 34.18 x 40.05 / top inset 1.05
BL outline 36.33 +/-0.1 x 43.45 +/-0.1
FPC extension 46.14 +/-0.5 / tail width 6.6 +/-0.05
LCD glass 36.13 x 43.25 / full LCM t=1.46 +/-0.1
21 contacts / center span 6 / pitch 0.3 / exposure 2.5
