0x616c6f6e/esp32s31-mp3/mechanical/enclosure-final-g/front-development.FCStd

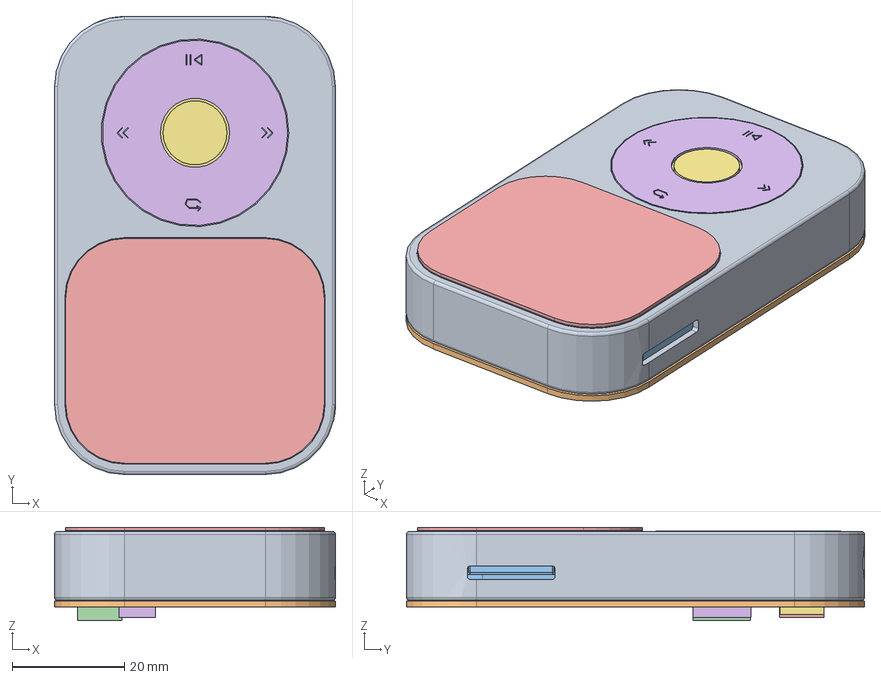
[picture p97: CAD file, 2026-09-24]
mechanical/enclosure-final-g/front-development.FCStd
50.0 x 81.5 x 16.6 mm
HousingControlsA
RearCoverWithPCBPosts
LCDModule
LCDActiveArea
CoverLens
LensBlackMask
LensAdhesive
ControlSymbols
DisplayFPCRoute
ControlBoardFasteners
MainPCB
WheelCopper
ControlFFC40mm
WheelControlsA
CenterButtonControlsA
C44 / C0402
C20 / C0402_1
C30 / C0402_1
C18 / C0603
X1 / CRYSTAL-SMD_4P-L3.2-W2.5-BL_1
C29 / C0402_1
C33 / C0402_1
R19 / R0402_1
R28 / R0402
C34 / C0402_1
C24 / C0402_1
CARD2 / TF-SMD_TF-PUSH
U5 / SOT-23-5_L3.0-W1.7-P0.95-LS2.8-BR_1
R9 / R0402
U3 / WQFN-24_L4.0-W4.0-P0.50-TL-EP2.7
C51 / C0402
C47 / C0402
U2 / QFN-40_L5.0-W5.0-P0.40-TL-EP3.6_1
U12 / TQFN-16_L3.0-W3.0-P0.50-BL-EP1.7
L2 / IND-SMD_L2.0-W1.6
U17 / MSOP-10_L3.0-W3.0-P0.50-LS4.9-BL
C16 / C0805
R17 / R0402_2
USB1 / USB-C-SMD_TYPE-C-16PIN-2MD-073
R31 / R0402
C11 / C0402
R18 / R0402_1
C15 / C0603_1
U7 / X2SON-8_L1.4-W1.0-P0.35-BL
R14 / R0402
C9 / C0603_1
U4 / SOT-23-5_L3.0-W1.7-P0.95-LS2.8-BR
C17 / C0402_1
R13 / R0402
R3 / R0402
C8 / C0603
C14 / C0603_1
C21 / C0402_1
U15 / LGA-14_L3.0-W2.5-P0.50-TL
R12 / R0402
C19 / C0402_1
C22 / C0402_1
C27 / C0402_1
C35 / C0402_1
C31 / C0402_1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
