0x616c6f6e/esp32s31-mp3/mechanical/enclosure-final-j/print-package/02-rear-cover.step

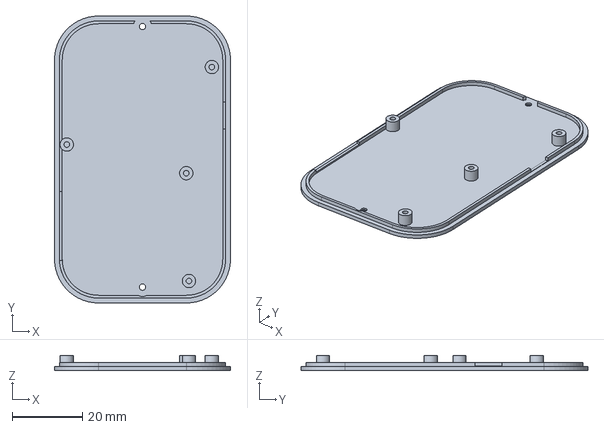
[picture p98: CAD file, 2026-09-24]
mechanical/enclosure-final-j/print-package/02-rear-cover.step
50.0 x 81.5 x 4.20 mm
