0x616c6f6e/esp32s31-mp3/mechanical/enclosure-final-k/print-package/01-housing.step

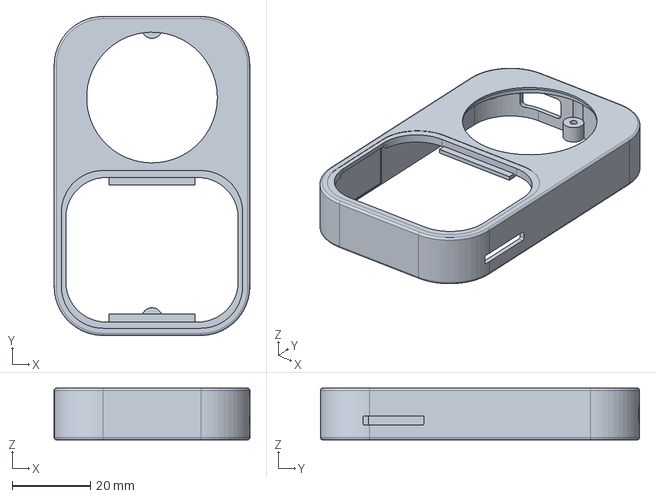
[picture p99: CAD file, 2026-09-24]
mechanical/enclosure-final-k/print-package/01-housing.step
50.0 x 81.5 x 13.2 mm
