0x616c6f6e/esp32s31-mp3/mechanical/enclosure-final-l/AM213Q410502LK-screen-stack.step

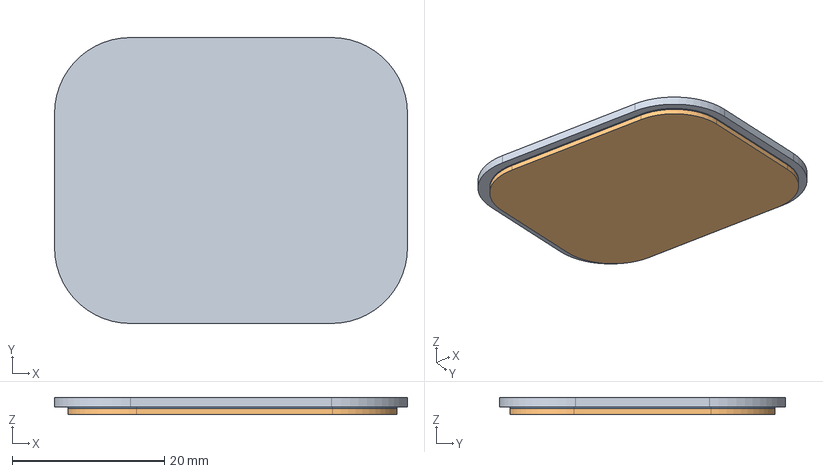
[picture p100: CAD file, 2026-09-24]
mechanical/enclosure-final-l/AM213Q410502LK-screen-stack.step
46.3 x 37.5 x 2.28 mm
AM213 integral touch cover / 46.30 x37.50 x1.30 / NOT extra glass
AM213 AMOLED panel / 43.14 x34.79 / stack excludes integral cover
Factory OCA bond / 0.175 mm
