0x616c6f6e/esp32s31-mp3/mechanical/enclosure-final-l/prototype-parts-not-released/05-motor-carrier.step

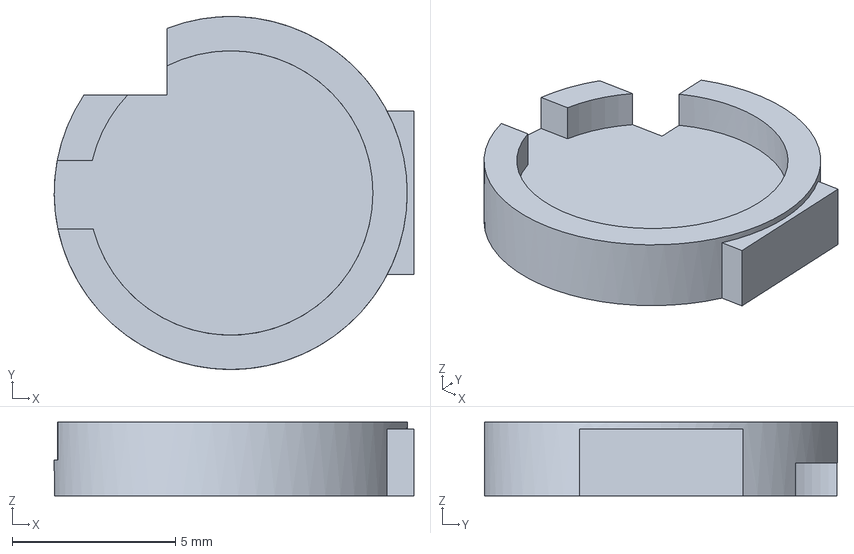
[picture p101: CAD file, 2026-09-24]
mechanical/enclosure-final-l/prototype-parts-not-released/05-motor-carrier.step
11.0 x 10.8 x 2.25 mm
