0x616c6f6e/esp32s31-mp3/mechanical/enclosure-q2-c/ESP32S31_MP3_Q2_C.FCStd

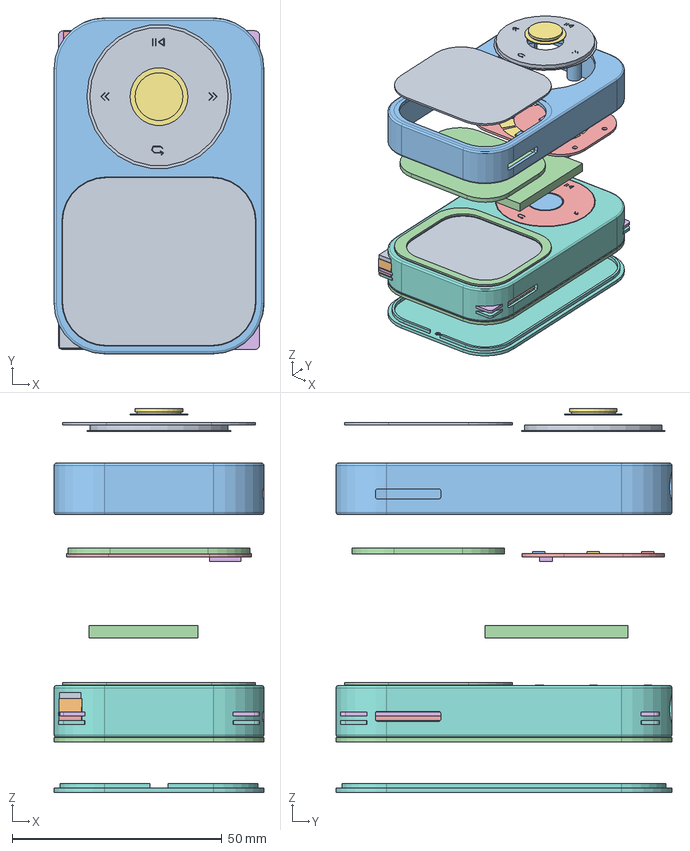
[picture p102: CAD file, 2026-09-21]
mechanical/enclosure-q2-c/ESP32S31_MP3_Q2_C.FCStd
50.0 x 80.0 x 91.5 mm
天线区域 / screen backing still needs RF review
电池占位 / 主板正面与操作板之间，26 x 34 x 3
独立滑环+五键板 / 44 x 34 x 0.8 / R10 / 4xD1.8
4 x M1.6 螺钉包络 / length and head TBD
操作板背面 FPC 座预留 / pin count TBD
操作板 FPC 通道 / 独立于屏幕排线
滑环电极位置示意 / 12 sectors, NOT copper design
按键图标 / return, previous, next, play-pause
屏幕排线通道与当前主板/元件相交
屏幕 FPC / 正面绕左板边至背面 FPC2
ESP32 / 主板正面，朝屏幕
电池占位 / 主板正面与操作板之间，26 x 34 x 001
独立滑环+五键板 / 44 x 34 x 0.8 / R10 / 4xD1.001
操作板背面 FPC 座预留 / pin count TBD001
滑环电极位置示意 / 12 sectors, NOT copper design001
按键图标 / return, previous, next, play-pause001
外加保护盖板 / 46 x 40 x 0.6 assumed, NOT supplied TP001
ESP32 / 主板正面，朝屏幕001
01 Q2 机身 / 独立操作板四点安装柱001
LCD 36.33 x 43.45 x 1.46 / rotated 90 degrees001
主板元件 / flipped together with PCB001
主板 / ESP32 面朝屏幕001
04 中心键 / 0.10 mm nominal actuator gap001
02 后盖 / two recessed M1.6 screws001
03 滑环面片 / four-way rocking actuator concept001
FPC2 / 主板背面屏幕连接器001
Back / 3 x 3 x 0.55 tact keepout, part TBD001
Next / 3 x 3 x 0.55 tact keepout, part TBD001
PlayPause / 3 x 3 x 0.55 tact keepout, part TBD001
Power / 3 x 3 x 0.55 tact keepout, part TBD001
Previous / 3 x 3 x 0.55 tact keepout, part TBD001
01 Q2 机身 / 独立操作板四点安装柱
LCD AA 34.18 x 40.05 / no touch layer supplied
LCD 36.33 x 43.45 x 1.46 / rotated 90 degrees
盖板周边胶框 / 0.18 mm assumed
盖板黑边示意 / silkscreen mask
主板元件 / flipped together with PCB
主板元件 / flipped together with PCB / 与壳体干涉
主板正面预留 FPC 座 / not present in current KiCad
主板 / ESP32 面朝屏幕
主板 / ESP32 面朝屏幕 / 与壳体干涉
新板机械空间 / 47 x 76 R10.5, not routed
04 中心键 / 0.10 mm nominal actuator gap
02 后盖 / two recessed M1.6 screws
03 滑环面片 / four-way rocking actuator concept
FPC2 / 主板背面屏幕连接器
Back / 3 x 3 x 0.55 tact keepout, part TBD
Next / 3 x 3 x 0.55 tact keepout, part TBD
PlayPause / 3 x 3 x 0.55 tact keepout, part TBD
Power / 3 x 3 x 0.55 tact keepout, part TBD
Previous / 3 x 3 x 0.55 tact keepout, part TBD
