0x616c6f6e/esp32s31-mp3/mechanical/enclosure-q2-c/exports/control-board-mechanical.step

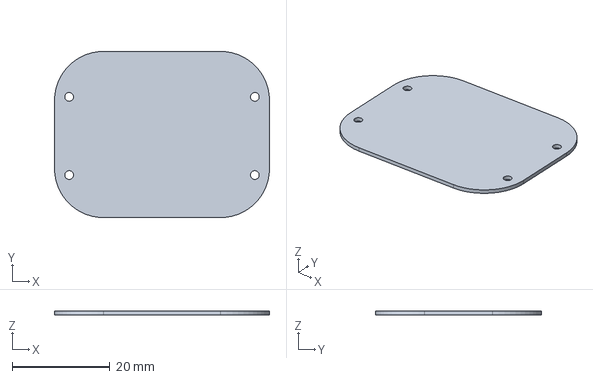
[picture p103: CAD file, 2026-09-21]
mechanical/enclosure-q2-c/exports/control-board-mechanical.step
44.0 x 34.0 x 0.8 mm
