0x616c6f6e/esp32s31-mp3/mechanical/enclosure-q2-d/ESP32S31_MP3_Q2_D.FCStd

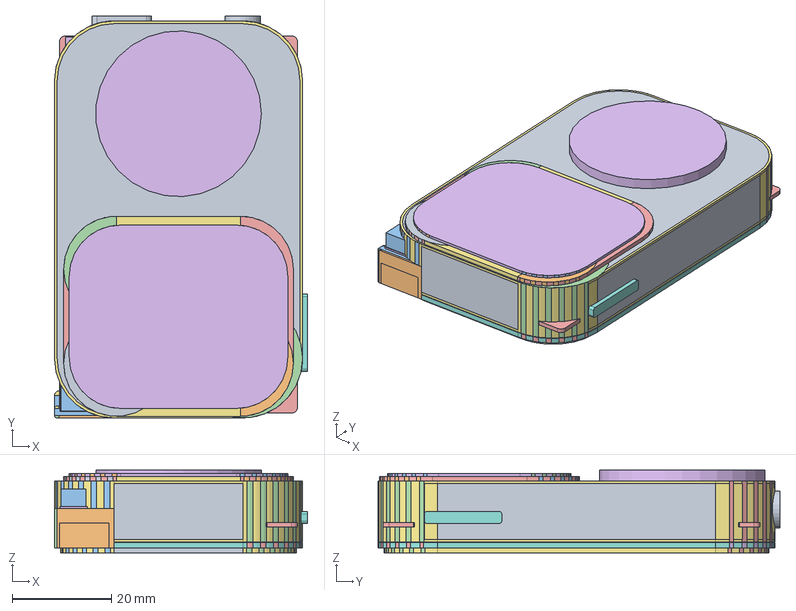
[picture p104: CAD file, 2026-09-21]
mechanical/enclosure-q2-d/ESP32S31_MP3_Q2_D.FCStd
51.0 x 81.0 x 16.7 mm
HousingBlankCoreX
HousingBlankCoreY
HousingBlankCorner0
HousingBlankCorner1
HousingBlankCorner2
HousingBlankCorner3
HousingBlank
HousingEdgeRoll
HousingCavityCoreX
HousingCavityCoreY
HousingCavityCorner0
HousingCavityCorner1
HousingCavityCorner2
HousingCavityCorner3
HousingCavity
HousingHollow
RearScrewBoss0
RearScrewPilot0
RearScrewSocket0
RearScrewBoss1
RearScrewPilot1
RearScrewSocket1
HousingWithBosses
LCDClearanceCoreX
LCDClearanceCoreY
LCDClearanceCorner0
LCDClearanceCorner1
LCDClearanceCorner2
LCDClearanceCorner3
LCDClearance
LensSeatCoreX
LensSeatCoreY
LensSeatCorner0
LensSeatCorner1
LensSeatCorner2
LensSeatCorner3
LensSeat
WheelSeat
CenterKeyHole
FrontCutter
HousingFrontOpenings
USBToolCoreX
USBToolCoreY
USBToolCorner0
USBToolCorner1
USBToolCorner2
USBToolCorner3
USBTool
JackTool
MicroSDToolCoreX
MicroSDToolCoreY
MicroSDToolCorner0
MicroSDToolCorner1
MicroSDToolCorner2
MicroSDToolCorner3
MicroSDTool
PortCutters
RearBlankCoreX
RearBlankCoreY
RearBlankCorner0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
