0x616c6f6e/esp32s31-mp3/mechanical/enclosure-q2-d/exports/q2-d-center-button.step

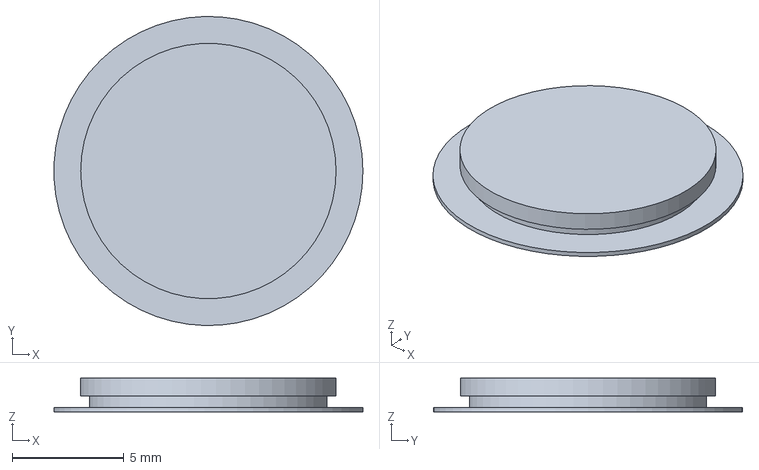
[picture p105: CAD file, 2026-09-21]
mechanical/enclosure-q2-d/exports/q2-d-center-button.step
13.8 x 13.8 x 1.50 mm
