0x616c6f6e/esp32s31-mp3/mechanical/enclosure-q2-e/ESP32S31_MP3_Q2_E.FCStd

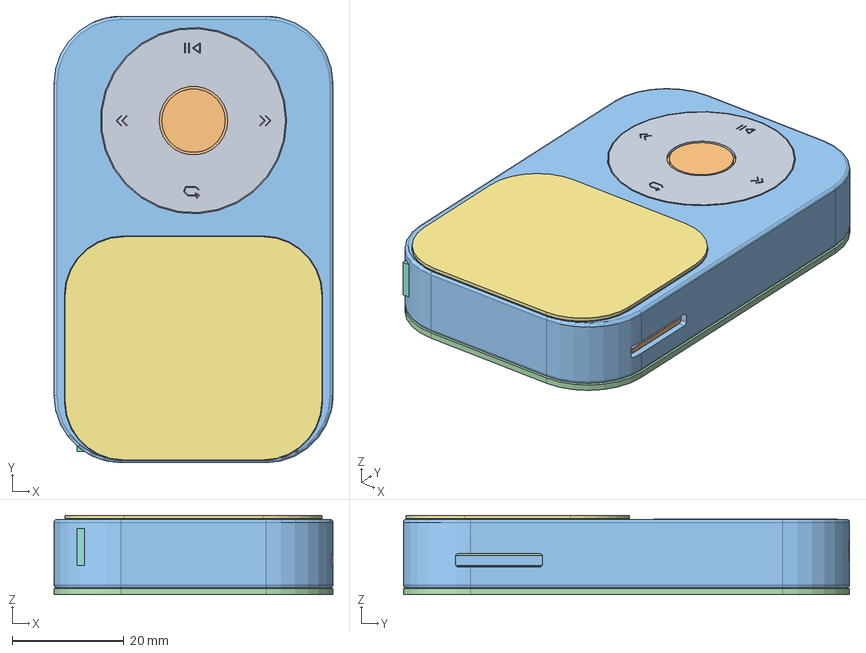
[picture p106: CAD file, 2026-09-21]
mechanical/enclosure-q2-e/ESP32S31_MP3_Q2_E.FCStd
50.0 x 80.0 x 14.2 mm
03 滑环面片 / four-way rocking actuator concept
04 中心键 / 0.10 mm nominal actuator gap
01 Q2 机身 / 独立操作板四点安装柱
02 Rear cover / four actual-PCB M2 support posts
LCD 36.33 x 43.45 x 1.46 / rotated 90 degrees
LCD AA 34.18 x 40.05 / no touch layer supplied
外加保护盖板 / 46 x 40 x 0.6 assumed, NOT supplied TP
盖板黑边示意 / silkscreen mask
盖板周边胶框 / 0.18 mm assumed
主板 / ESP32 面朝屏幕
主板元件 / flipped together with PCB
ESP32 / 主板正面，朝屏幕
FPC2 / rear / verified 1.0 mm height
新板机械空间 / 46 x76 R10 clearance reference; actual routed board is MainPCB
电池占位 / 主板正面与操作板之间，24 x 34 x 3
天线区域 / screen backing still needs RF review
独立滑环+五键板 / 44 x 34 x 0.8 / R10 / 4xD1.8
Power / 3 x 3 x 0.55 tact keepout, part TBD
Back / 3 x 3 x 0.55 tact keepout, part TBD
Previous / 3 x 3 x 0.55 tact keepout, part TBD
Next / 3 x 3 x 0.55 tact keepout, part TBD
PlayPause / 3 x 3 x 0.55 tact keepout, part TBD
滑环电极位置示意 / 12 sectors, NOT copper design
操作板背面 FPC 座预留 / pin count TBD
主板正面预留 FPC 座 / not present in current KiCad
4 x M1.6 螺钉包络 / length and head TBD
屏幕 FPC / 上移1.5 mm后的自然轴线，尚未插接
操作板 FPC 通道 / 独立于屏幕排线
按键图标 / return, previous, next, play-pause
