0x616c6f6e/esp32s31-mp3/mechanical/enclosure-q2-f/ESP32S31_MP3_Q2_F.FCStd

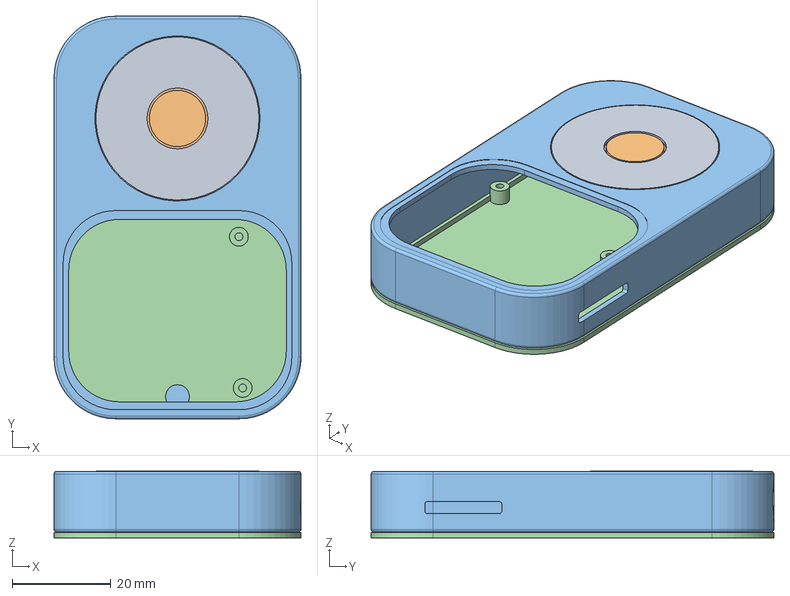
[picture p107: CAD file, 2026-09-24]
mechanical/enclosure-q2-f/ESP32S31_MP3_Q2_F.FCStd
50.0 x 81.5 x 13.5 mm
03 滑环面片 / four-way rocking actuator concept
04 中心键 / 0.10 mm nominal actuator gap
01 Q2 机身 / 独立操作板四点安装柱
02 Rear cover / four actual-PCB M2 support posts
