0x616c6f6e/esp32s31-mp3/mechanical/enclosure-q2-f/exports/q2-f-housing.step

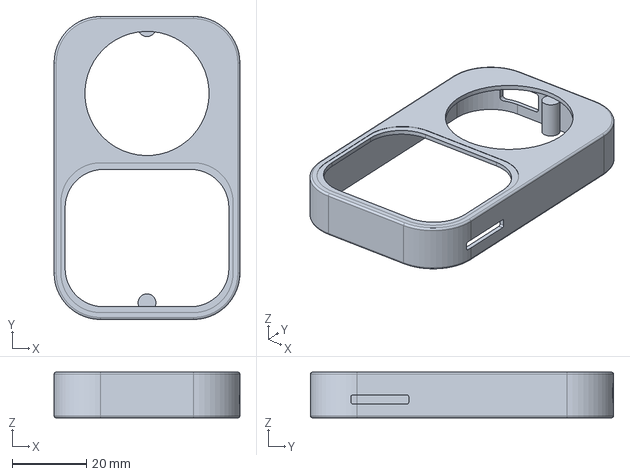
[picture p108: CAD file, 2026-09-21]
mechanical/enclosure-q2-f/exports/q2-f-housing.step
50.0 x 81.5 x 12.3 mm
