0x616c6f6e/esp32s31-mp3/mechanical/enclosure-q2/ESP32S31_MP3_Q2_B.FCStd

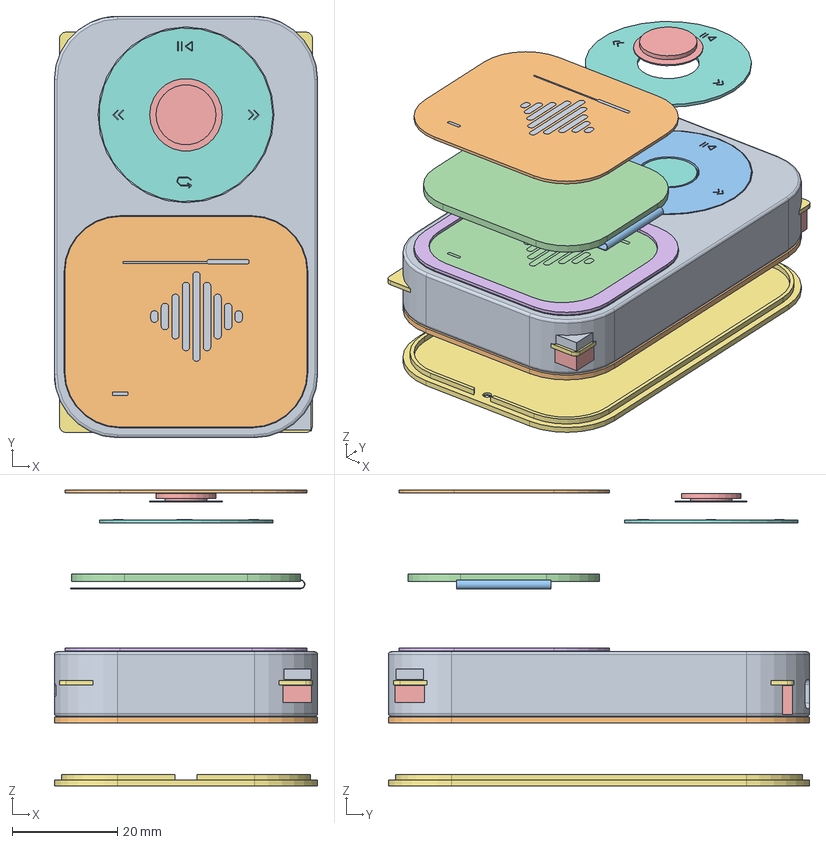
[picture p109: CAD file, 2026-09-21]
mechanical/enclosure-q2/ESP32S31_MP3_Q2_B.FCStd
50.0 x 80.0 x 56.2 mm
现有天线区域 / screen overlap requires RF review
电池占位 26 x 34 x 3 / unconfirmed
中心开关预留 / wire to KEY+GND, select real switch
按键图标 / return, previous, next, play-pause
现有器件包络 / heights assumed
红色实体：现有器件包络 / heights assumed 与新壳干涉
现有 PCB / clashes with Q2 corners
红色实体：现有 PCB / clashes with Q2 corners 与新壳干涉
按键图标 / return, previous, next, play-pause001
外加保护盖板 / 46 x 40 x 0.6 assumed, NOT supplied TP001
FPC 46.14 mm / one-fold routing STUDY, connector not mated001
LCD 36.33 x 43.45 x 1.46 / rotated 90 degrees001
04 中心电源键 / switch travel must be tuned001
01 Q2 大圆角机身 / prototype, PCB redesign required001
02 后盖 / two recessed M1.6 screws001
03 黑色操作环面片 / sensor electronics pending001
屏幕示意图 / cosmetic only, not exported001
FPC 46.14 mm / one-fold routing STUDY, connector not mated
LCD AA 34.18 x 40.05 / no touch layer supplied
LCD 36.33 x 43.45 x 1.46 / rotated 90 degrees
盖板周边胶框 / 0.18 mm assumed
盖板黑边示意 / silkscreen mask
PCB 新轮廓建议 / constraint solid only, NOT routed board
04 中心电源键 / switch travel must be tuned
01 Q2 大圆角机身 / prototype, PCB redesign required
02 后盖 / two recessed M1.6 screws
03 黑色操作环面片 / sensor electronics pending
屏幕示意图 / cosmetic only, not exported
操作环电路预留 / main PCB has no wheel circuit
