0x616c6f6e/esp32s31-mp3/mechanical/enclosure-q2/exports/q2-housing.step

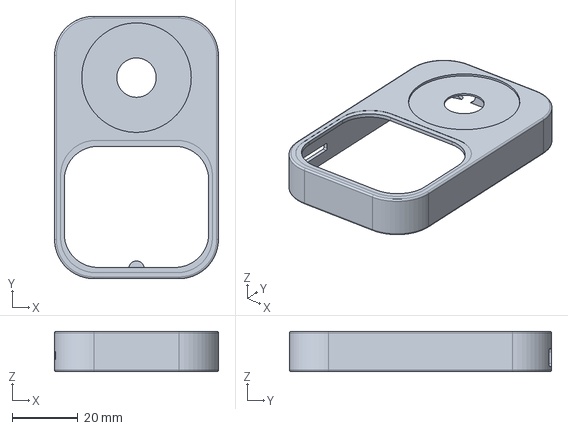
[picture p110: CAD file, 2026-09-21]
mechanical/enclosure-q2/exports/q2-housing.step
50.0 x 80.0 x 12.3 mm
