0x616c6f6e/esp32s31-mp3/mechanical/enclosure/ESP32S31_MP3_Enclosure_A.FCStd

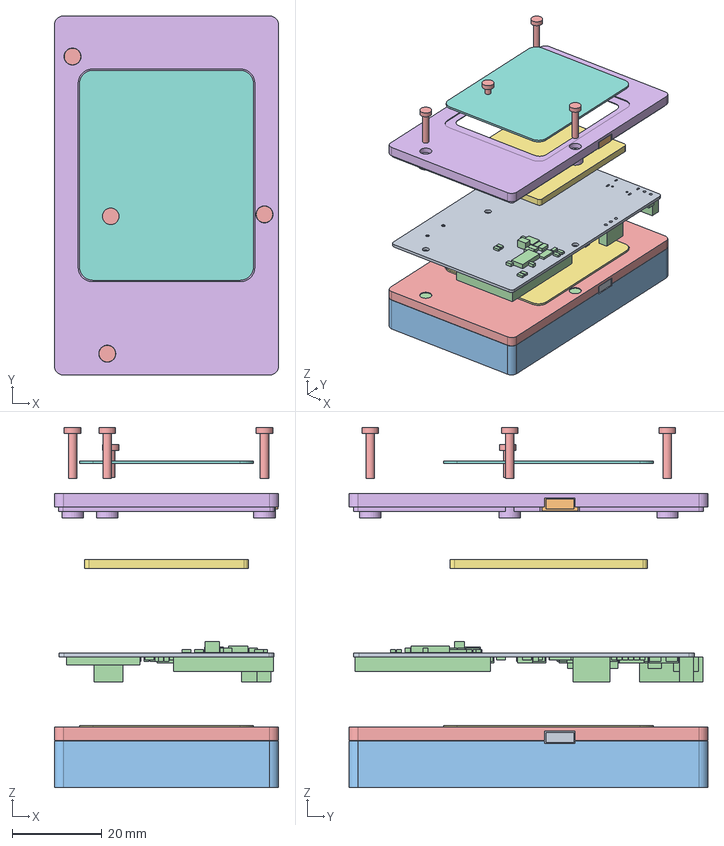
[picture p111: CAD file, 2026-09-21]
mechanical/enclosure/ESP32S31_MP3_Enclosure_A.FCStd
50.0 x 80.0 x 80.3 mm
ASSUMED battery / 26 x 34 x 3 mm
ASSUMED component heights / 122 bounding envelopes
ASSUMED battery / 26 x 34 x 3 mm001
ASSUMED component heights / 122 bounding envelopes001
3 x M2x10 + 1 x M2x6 / assumed low heads001
02 前盖 / screen bezel001
ASSUMED LCD envelope001
ASSUMED cover lens001
PCB - imported KiCad body, read only001
03 电源键 / flush cap001
01 后壳 / 0.75 mm resin prototype001
3 x M2x10 + 1 x M2x6 / assumed low heads
02 前盖 / screen bezel
ASSUMED LCD envelope
ASSUMED cover lens
PCB - imported KiCad body, read only
03 电源键 / flush cap
ASSUMED wired power tact switch
01 后壳 / 0.75 mm resin prototype
