0x616c6f6e/esp32s31-mp3/mechanical/final-board-review/models3d/U10-nominal-envelope.step

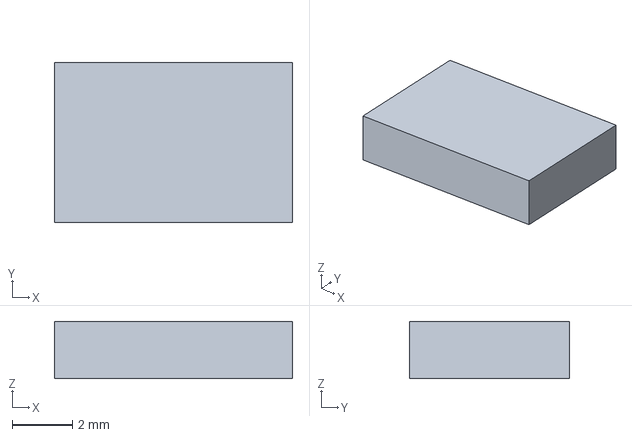
[picture p112: CAD file, 2026-09-24]
mechanical/final-board-review/models3d/U10-nominal-envelope.step
7.90 x 5.30 x 1.90 mm
