0x616c6f6e/esp32s31-mp3/mechanical/final-board-review/WheelControlsA.step

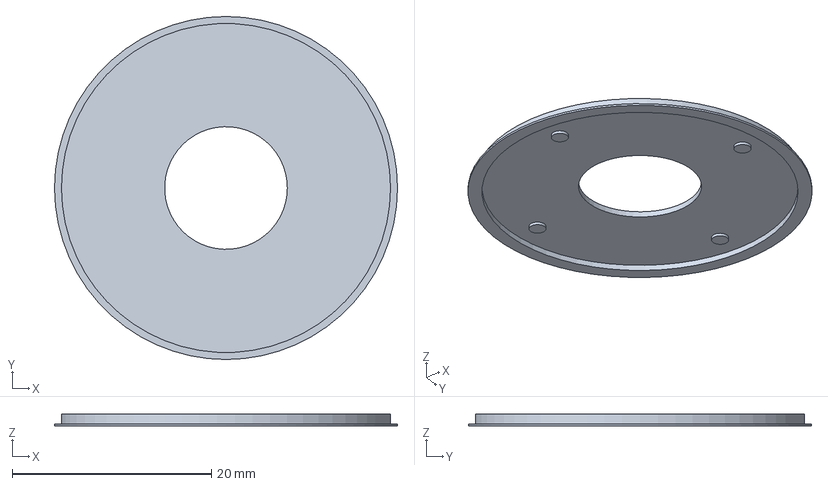
[picture p113: CAD file, 2026-09-24]
mechanical/final-board-review/WheelControlsA.step
34.4 x 34.4 x 1.20 mm
