0x616c6f6e/esp32s31-mp3/mechanical/Q2-appearance-prototype-v2/print-parts/01-body.stl

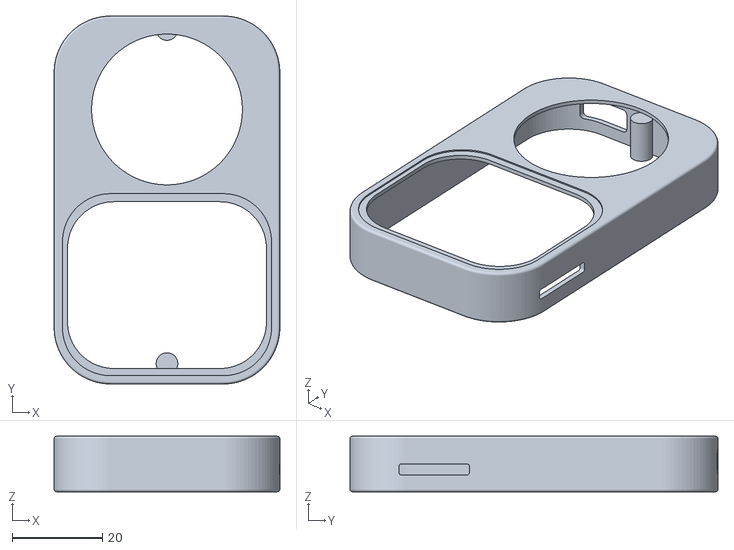
[picture p114: CAD file, 2026-09-24]
mechanical/Q2-appearance-prototype-v2/print-parts/01-body.stl
50.0 x 81.5 x 12.3
