0x616c6f6e/esp32s31-mp3/mechanical/Q2-appearance-prototype-v2/reference/03-wheel.step

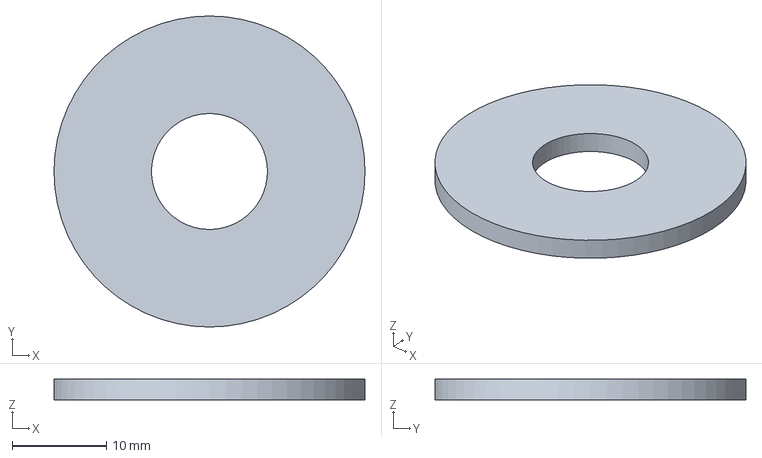
[picture p115: CAD file, 2026-09-24]
mechanical/Q2-appearance-prototype-v2/reference/03-wheel.step
33.0 x 33.0 x 2.20 mm
