0x616c6f6e/esp32s31-mp3/mechanical/v2-btb-placement/Q2_V2_BTB_Position_Study.FCStd

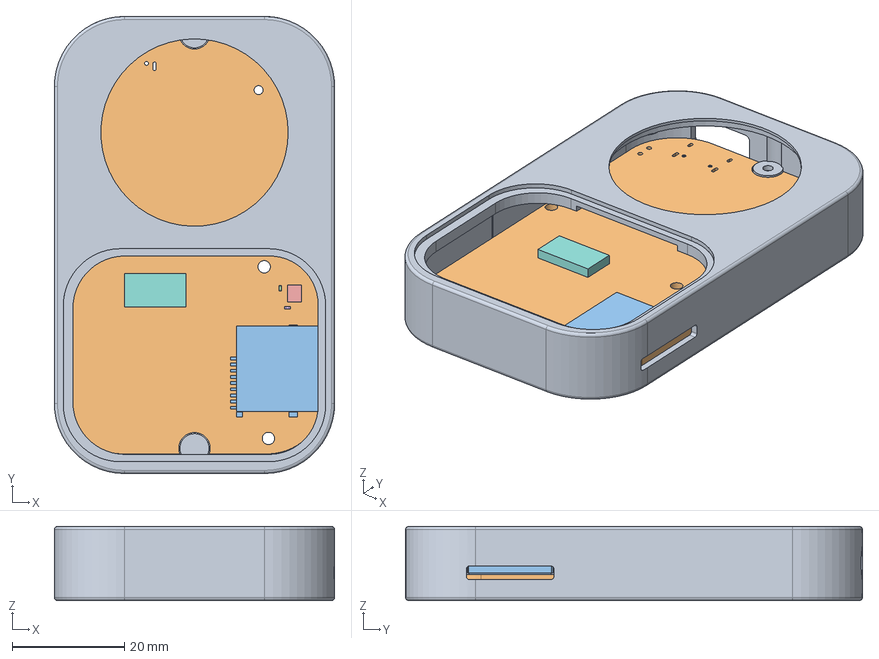
[picture p116: CAD file, 2026-09-24]
mechanical/v2-btb-placement/Q2_V2_BTB_Position_Study.FCStd
50.0 x 81.5 x 13.2 mm
01 Housing L / AM213 integrated cover aperture
MainPCB
CARD2 / TF-SMD_TF-PUSH
C47 / C0402
U15 / LGA-14_L3.0-W2.5-P0.50-TL
C48 / C0402
V2 candidate / OK-23GF024-04 / mainboard FRONT / NOT frozen
11x6 placement & access reservation / engineering allowance
