0x616c6f6e/esp32s31-mp3/hardware-controls/mechanical/CenterButtonControlsA.step

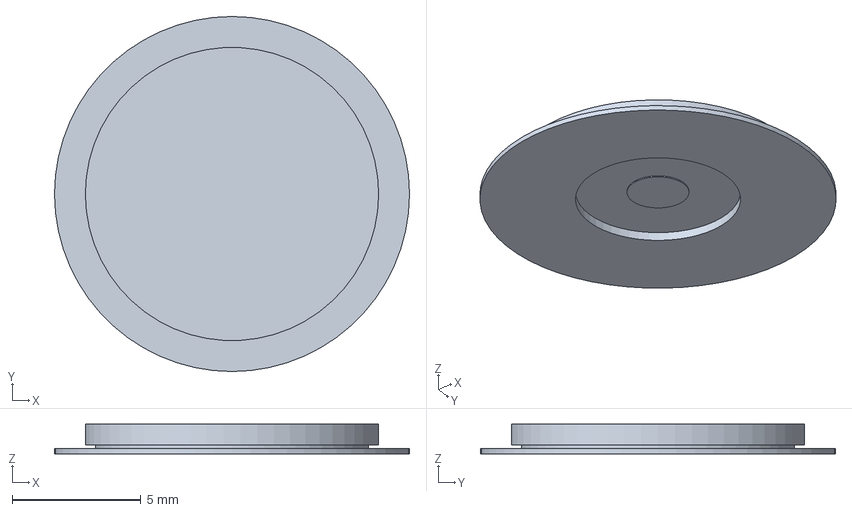
[picture p117: CAD file, 2026-09-24]
hardware-controls/mechanical/CenterButtonControlsA.step
13.8 x 13.8 x 1.15 mm
