0x616c6f6e/esp32s31-mp3/hardware-controls/models3d/SKSW_3x2.step

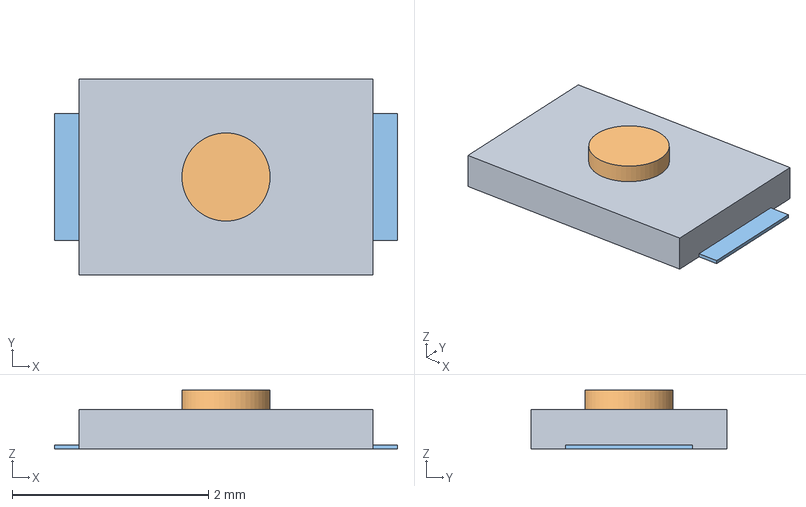
[picture p118: CAD file, 2026-09-24]
hardware-controls/models3d/SKSW_3x2.step
3.50 x 2.00 x 0.6 mm
SKSW_3x2_0
SKSW_3x2_1
SKSW_3x2_2
SKSW_3x2_3
