0x616c6f6e/esp32s31-mp3/hardware-controls/output/ch32v006-review/before/models3d/TCA6408A_VQFN16.step

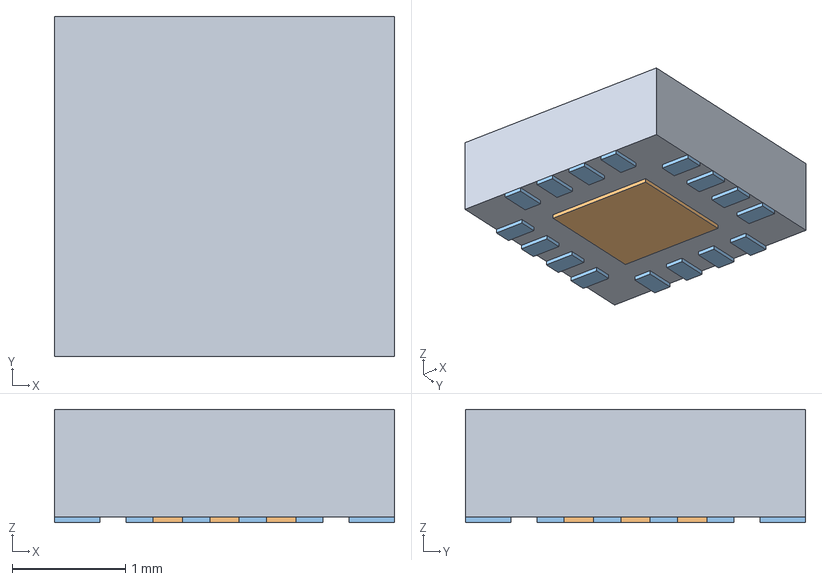
[picture p119: CAD file, 2026-09-24]
hardware-controls/output/ch32v006-review/before/models3d/TCA6408A_VQFN16.step
3.00 x 3.00 x 1.00 mm
TCA6408A_VQFN16_0
TCA6408A_VQFN16_1
TCA6408A_VQFN16_2
TCA6408A_VQFN16_3
TCA6408A_VQFN16_4
TCA6408A_VQFN16_5
TCA6408A_VQFN16_6
TCA6408A_VQFN16_7
TCA6408A_VQFN16_8
TCA6408A_VQFN16_9
TCA6408A_VQFN16_10
TCA6408A_VQFN16_11
TCA6408A_VQFN16_12
TCA6408A_VQFN16_13
TCA6408A_VQFN16_14
TCA6408A_VQFN16_15
TCA6408A_VQFN16_16
TCA6408A_VQFN16_17
