0x616c6f6e/esp32s31-mp3/hardware-controls/output/controls-populated.step

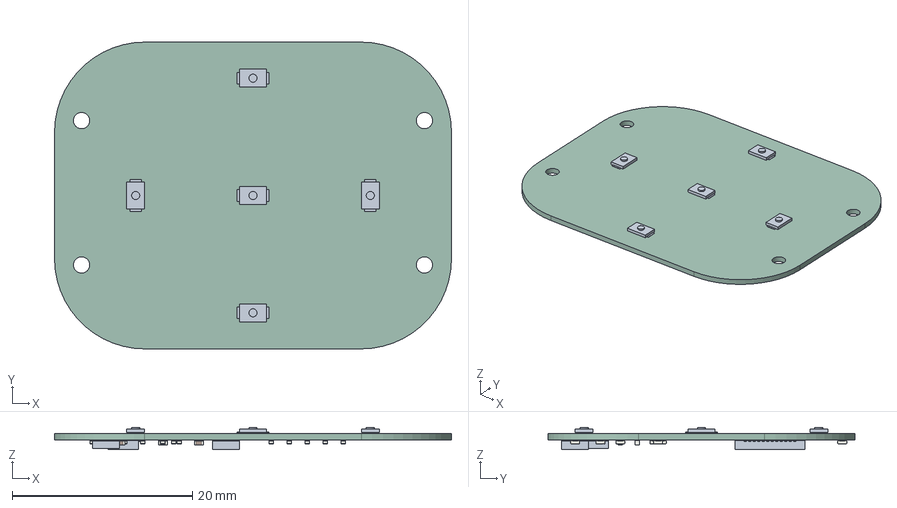
[picture p120: CAD file, 2026-09-24]
hardware-controls/output/controls-populated.step
44.0 x 34.0 x 2.48 mm
SKSW_3x2_0 x 5
SKSW_3x2_1 x 5
SKSW_3x2_2 x 5
SKSW_3x2_3 x 5
QT2120_VQFN20_0
QT2120_VQFN20_1
QT2120_VQFN20_2
QT2120_VQFN20_3
QT2120_VQFN20_4
QT2120_VQFN20_5
QT2120_VQFN20_6
QT2120_VQFN20_7
QT2120_VQFN20_8
QT2120_VQFN20_9
QT2120_VQFN20_10
QT2120_VQFN20_11
QT2120_VQFN20_12
QT2120_VQFN20_13
QT2120_VQFN20_14
QT2120_VQFN20_15
QT2120_VQFN20_16
QT2120_VQFN20_17
QT2120_VQFN20_18
QT2120_VQFN20_19
QT2120_VQFN20_20
QT2120_VQFN20_21
C_0402_1005Metric x 4
R_0402_1005Metric x 14
TCA6408A_VQFN16_0
TCA6408A_VQFN16_1
TCA6408A_VQFN16_2
TCA6408A_VQFN16_3
TCA6408A_VQFN16_4
TCA6408A_VQFN16_5
TCA6408A_VQFN16_6
TCA6408A_VQFN16_7
TCA6408A_VQFN16_8
TCA6408A_VQFN16_9
TCA6408A_VQFN16_10
TCA6408A_VQFN16_11
TCA6408A_VQFN16_12
TCA6408A_VQFN16_13
TCA6408A_VQFN16_14
TCA6408A_VQFN16_15
TCA6408A_VQFN16_16
TCA6408A_VQFN16_17
Housing
Latch
Pin1
Pin2
Pin3
Pin4
Pin5
Pin6
Pin7
Pin8
Pin9
Pin10
Pin11
Pin12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
