0x616c6f6e/esp32s31-mp3/hardware-display-adapter/am213-fpc-adapter/models3d/adapter-with-btb.step

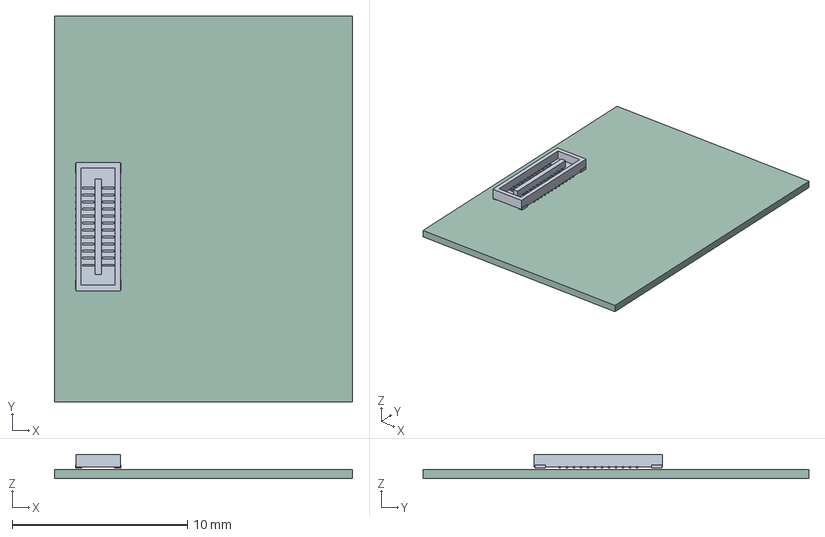
[picture p121: CAD file, 2026-09-24]
hardware-display-adapter/am213-fpc-adapter/models3d/adapter-with-btb.step
17.0 x 22.0 x 1.39 mm
am213-fpc-adapter_PCB
