0x616c6f6e/esp32s31-mp3/hardware-display-adapter/am213-fpc-adapter/output/folded-tail.step

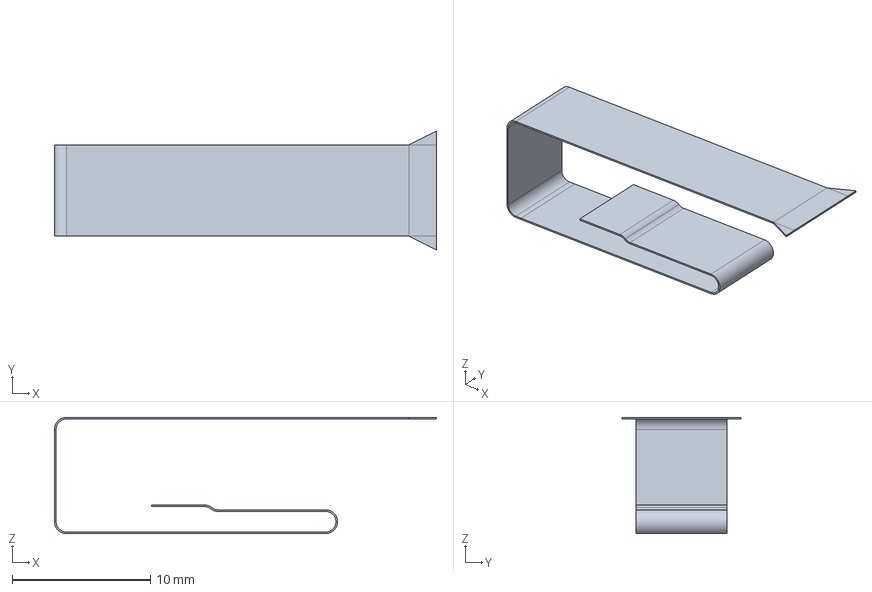
[picture p122: CAD file, 2026-09-24]
hardware-display-adapter/am213-fpc-adapter/output/folded-tail.step
27.7 x 8.60 x 8.41 mm
