0x616c6f6e/esp32s31-mp3/hardware-q2-v2/models3d/Crystal_3225_H065_nominal.step

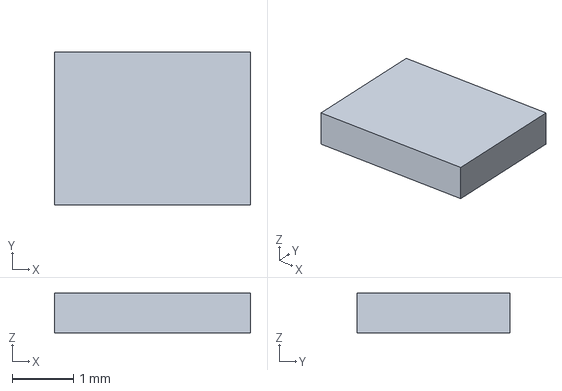
[picture p123: CAD file, 2026-09-24]
hardware-q2-v2/models3d/Crystal_3225_H065_nominal.step
3.20 x 2.50 x 0.65 mm
