0x616c6f6e/esp32s31-mp3/mechanical/enclosure-final-j/print-package/03-wheel-with-carrier.step

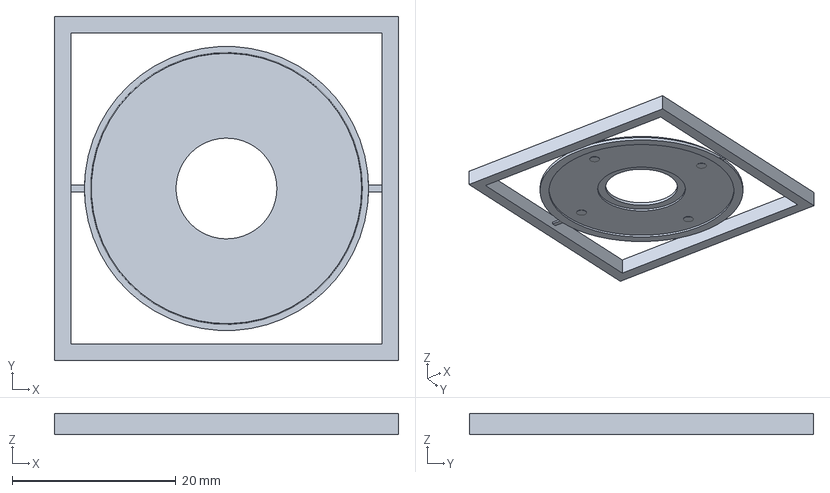
[picture p125: CAD file, 2026-09-24]
mechanical/enclosure-final-j/print-package/03-wheel-with-carrier.step
42.0 x 42.0 x 2.60 mm
