0x616c6f6e/esp32s31-mp3/mechanical/enclosure-final-k/print-package/03-wheel.step

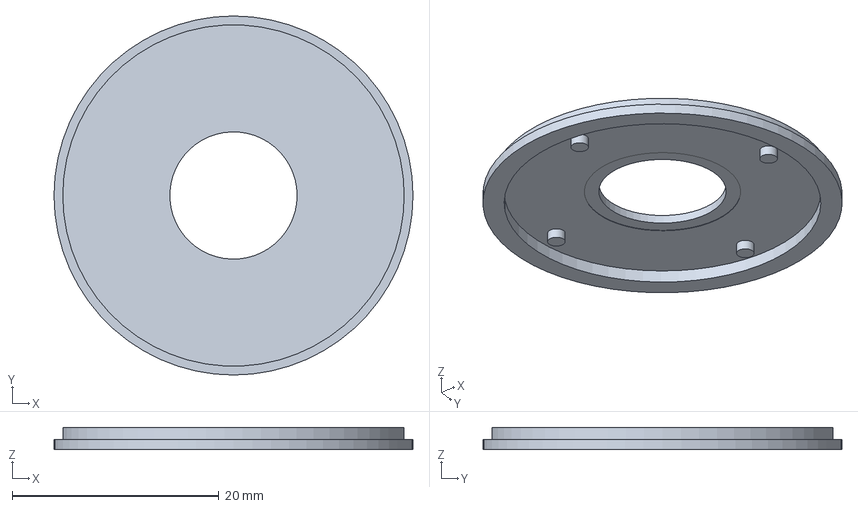
[picture p126: CAD file, 2026-09-24]
mechanical/enclosure-final-k/print-package/03-wheel.step
34.7 x 34.7 x 2.15 mm
