0x616c6f6e/esp32s31-mp3/mechanical/enclosure-final-l/prototype-parts-not-released/06-insert-fit-coupon-optional.step

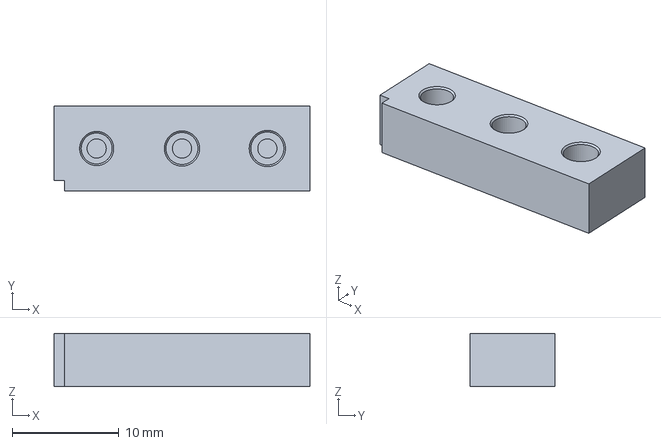
[picture p127: CAD file, 2026-09-24]
mechanical/enclosure-final-l/prototype-parts-not-released/06-insert-fit-coupon-optional.step
24.0 x 8.00 x 5.00 mm
