0x616c6f6e/esp32s31-mp3/mechanical/enclosure-q2-c/exports/q2-c-wheel-rocker.step

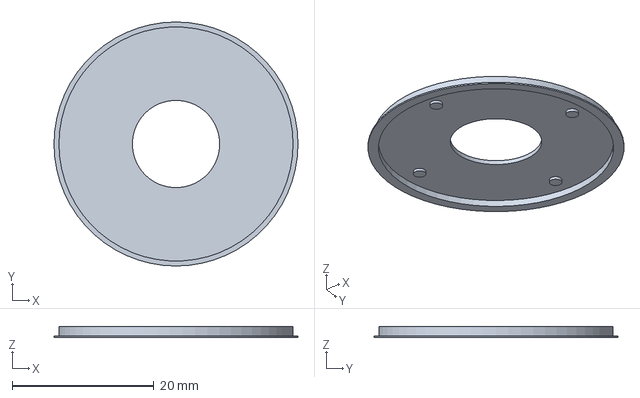
[picture p129: CAD file, 2026-09-21]
mechanical/enclosure-q2-c/exports/q2-c-wheel-rocker.step
34.4 x 34.4 x 1.52 mm
