0x616c6f6e/esp32s31-mp3/mechanical/enclosure-q2-d/exports/q2-d-housing.step

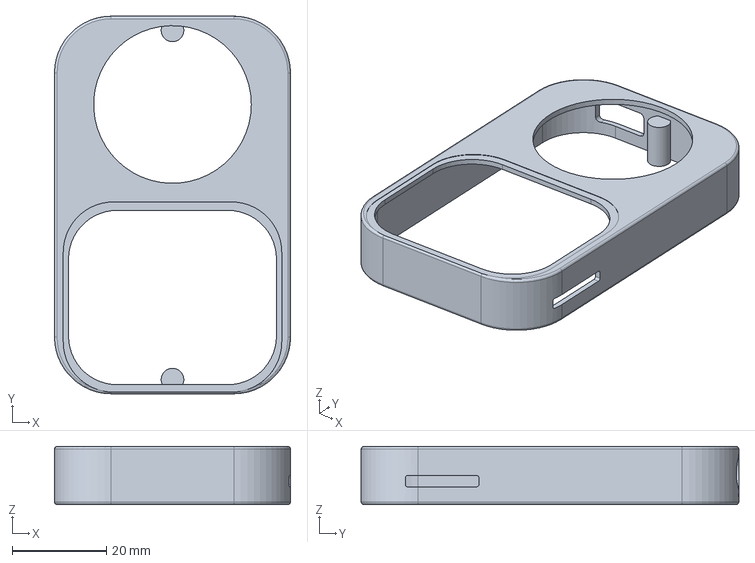
[picture p130: CAD file, 2026-09-21]
mechanical/enclosure-q2-d/exports/q2-d-housing.step
50.0 x 80.0 x 12.3 mm
