0x616c6f6e/esp32s31-mp3/mechanical/enclosure-q2-f/exports/q2-f-rear-cover.step

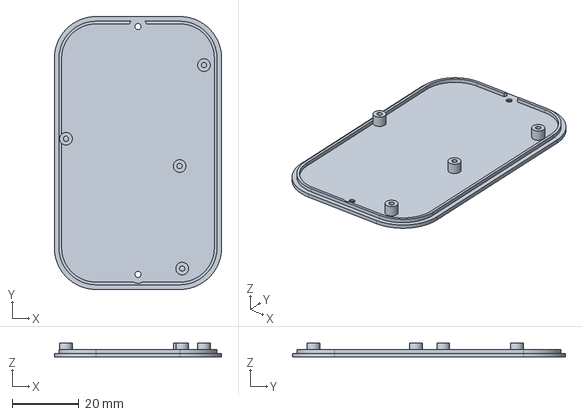
[picture p131: CAD file, 2026-09-21]
mechanical/enclosure-q2-f/exports/q2-f-rear-cover.step
50.0 x 81.5 x 4.20 mm
