0x616c6f6e/esp32s31-mp3/mechanical/enclosure-q2/exports/cover-lens-assumed.step

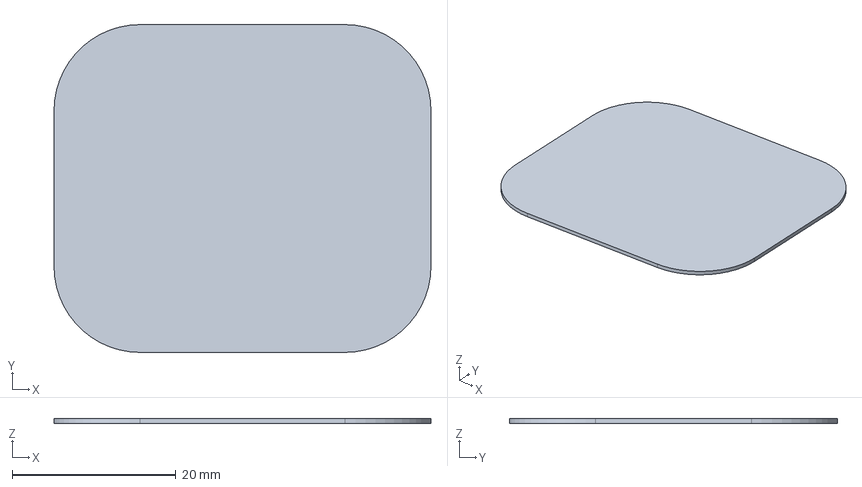
[picture p132: CAD file, 2026-09-21]
mechanical/enclosure-q2/exports/cover-lens-assumed.step
46.0 x 40.0 x 0.6 mm
