0x616c6f6e/esp32s31-mp3/mechanical/enclosure/exports/power-button.step

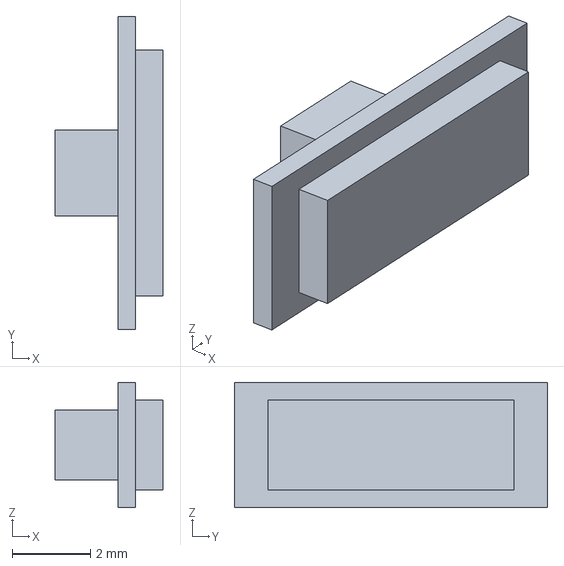
[picture p133: CAD file, 2026-09-21]
mechanical/enclosure/exports/power-button.step
2.75 x 8.00 x 3.20 mm
