0x616c6f6e/esp32s31-mp3/mechanical/final-board-review/models3d/JST_ACH_BM03B-ACHSS-GAN-ETF_1x03-1MP_P1.20mm_Vertical.step

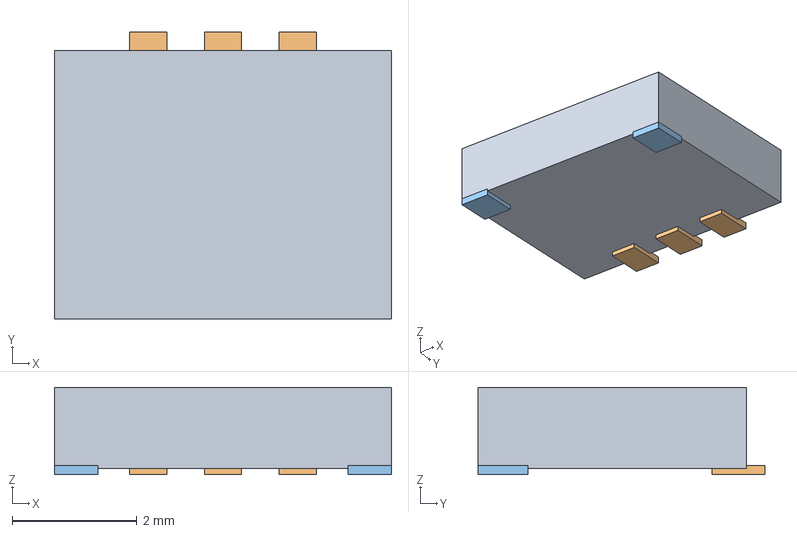
[picture p134: CAD file, 2026-09-21]
mechanical/final-board-review/models3d/JST_ACH_BM03B-ACHSS-GAN-ETF_1x03-1MP_P1.20mm_Vertical.step
5.40 x 4.60 x 1.40 mm
