0x616c6f6e/esp32s31-mp3/hardware-controls/output/ch32v006-review/before/models3d/QT2120_VQFN20.step

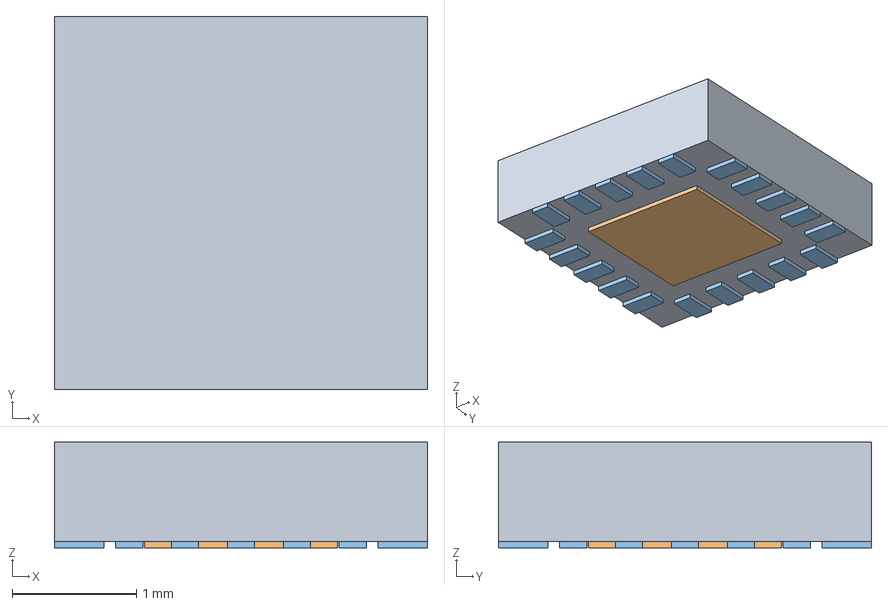
[picture p135: CAD file, 2026-09-24]
hardware-controls/output/ch32v006-review/before/models3d/QT2120_VQFN20.step
3.00 x 3.00 x 0.85 mm
QT2120_VQFN20_0
QT2120_VQFN20_1
QT2120_VQFN20_2
QT2120_VQFN20_3
QT2120_VQFN20_4
QT2120_VQFN20_5
QT2120_VQFN20_6
QT2120_VQFN20_7
QT2120_VQFN20_8
QT2120_VQFN20_9
QT2120_VQFN20_10
QT2120_VQFN20_11
QT2120_VQFN20_12
QT2120_VQFN20_13
QT2120_VQFN20_14
QT2120_VQFN20_15
QT2120_VQFN20_16
QT2120_VQFN20_17
QT2120_VQFN20_18
QT2120_VQFN20_19
QT2120_VQFN20_20
QT2120_VQFN20_21
