0x616c6f6e/esp32s31-mp3/hardware-q2-v2/models3d/OK-23GF024-04.step

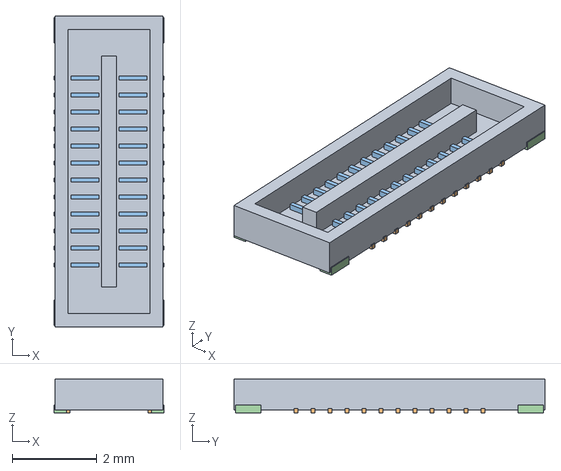
[picture p136: CAD file, 2026-09-24]
hardware-q2-v2/models3d/OK-23GF024-04.step
2.59 x 7.32 x 0.79 mm
