0x616c6f6e/esp32s31-mp3/mechanical/display-fit/exports/AFE03-21-envelope.step

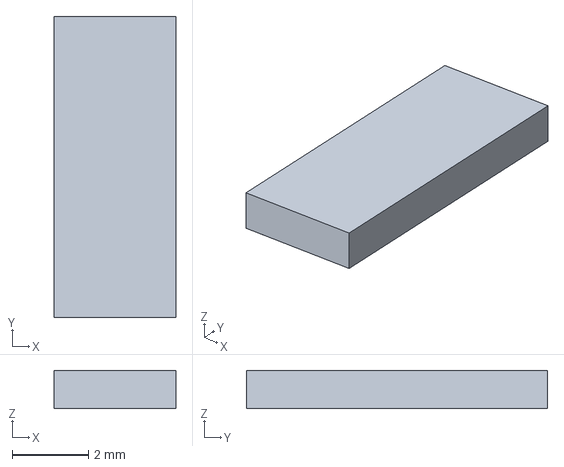
[picture p137: CAD file, 2026-09-21]
mechanical/display-fit/exports/AFE03-21-envelope.step
3.20 x 7.90 x 1.00 mm
