0x616c6f6e/esp32s31-mp3/mechanical/enclosure-q2-d/exports/q2-d-rear-cover.step

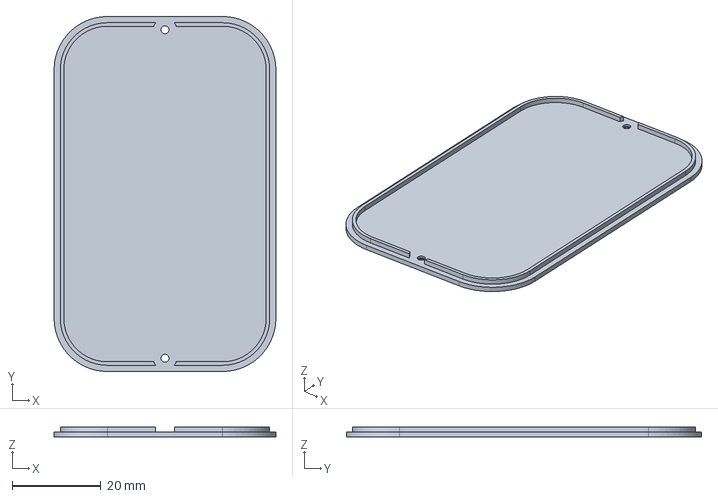
[picture p139: CAD file, 2026-09-21]
mechanical/enclosure-q2-d/exports/q2-d-rear-cover.step
50.0 x 80.0 x 2.20 mm
