0x616c6f6e/esp32s31-mp3/mechanical/enclosure/exports/front-shell.step

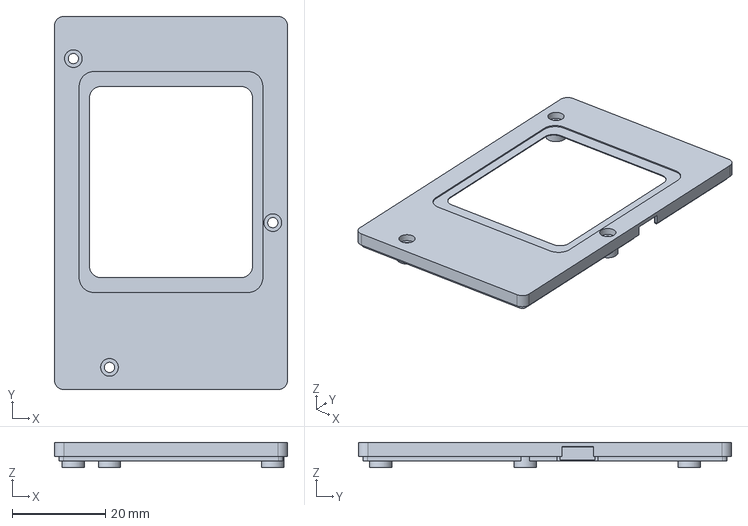
[picture p140: CAD file, 2026-09-21]
mechanical/enclosure/exports/front-shell.step
50.0 x 80.0 x 5.40 mm
