0x616c6f6e/esp32s31-mp3/mechanical/final-board-review/models3d/JST_ACH_BM02B-ACHSS-GAN-ETF_1x02-1MP_P1.20mm_Vertical.step

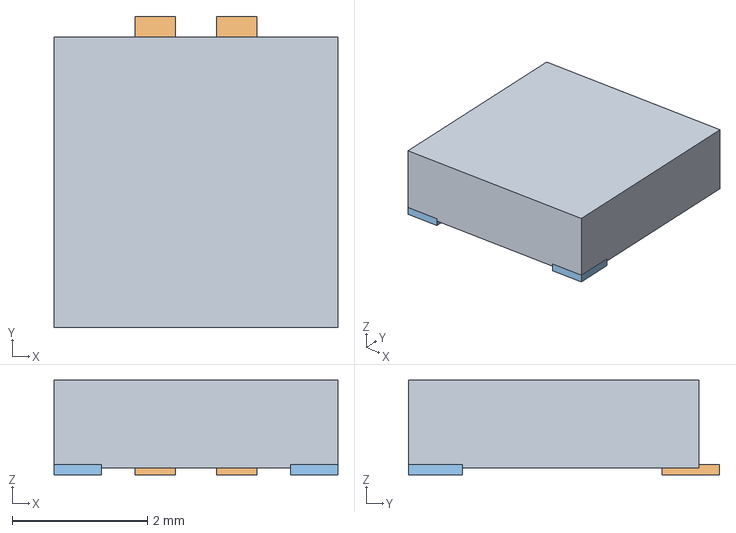
[picture p141: CAD file, 2026-09-21]
mechanical/final-board-review/models3d/JST_ACH_BM02B-ACHSS-GAN-ETF_1x02-1MP_P1.20mm_Vertical.step
4.20 x 4.60 x 1.40 mm
