0x616c6f6e/esp32s31-mp3/hardware-display-adapter/am213-fpc-adapter/models3d/OK-23GF024-04.FCStd

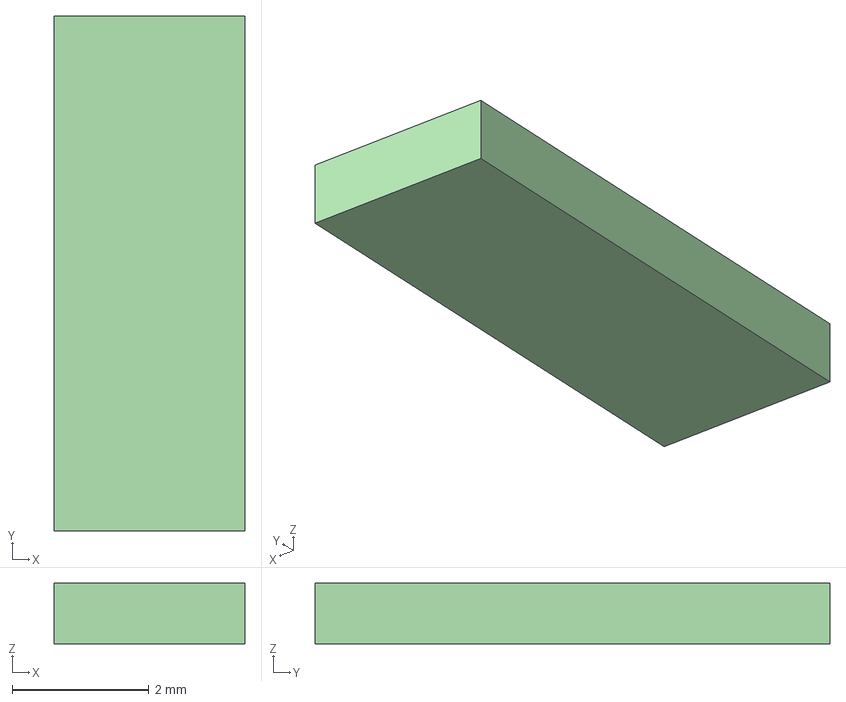
[picture p142: CAD file, 2026-09-24]
hardware-display-adapter/am213-fpc-adapter/models3d/OK-23GF024-04.FCStd
2.79 x 7.52 x 0.89 mm
Housing
24 contacts / schematic, not numbered
Retention clips / simplified
Maximum dimensional envelope / not physical solid
