0x616c6f6e/esp32s31-mp3/hardware-q2-v2/models3d/HCTL_FPC12.step

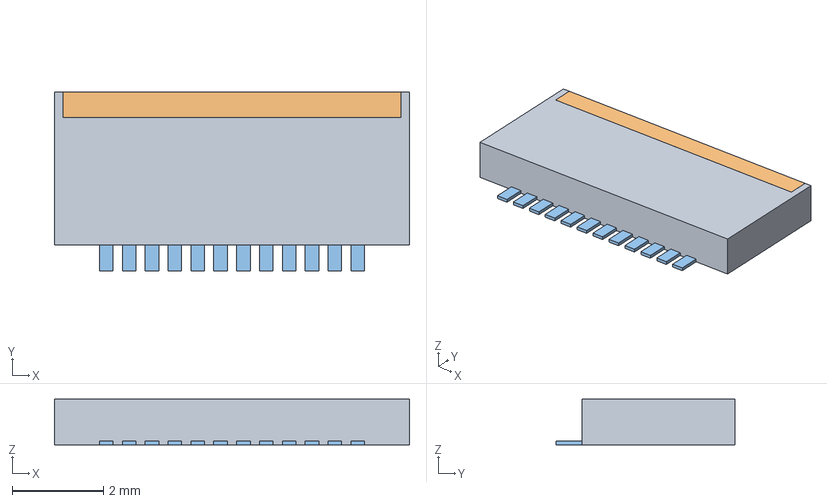
[picture p143: CAD file, 2026-09-24]
hardware-q2-v2/models3d/HCTL_FPC12.step
7.77 x 3.91 x 1.00 mm
Housing
Latch
Pin1
Pin2
Pin3
Pin4
Pin5
Pin6
Pin7
Pin8
Pin9
Pin10
Pin11
Pin12
Mount
Mount001
