0x616c6f6e/esp32s31-mp3/mechanical/enclosure-final-j/print-package/04-center-with-carrier.step

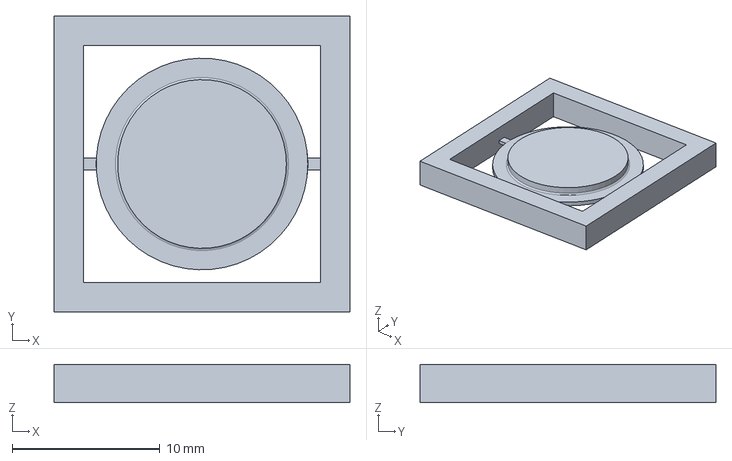
[picture p144: CAD file, 2026-09-24]
mechanical/enclosure-final-j/print-package/04-center-with-carrier.step
20.0 x 20.0 x 2.60 mm
