0x616c6f6e/esp32s31-mp3/mechanical/enclosure-final-k/print-package/04-center-button.step

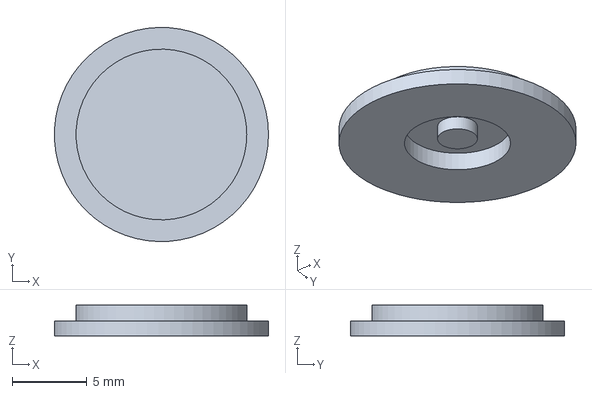
[picture p145: CAD file, 2026-09-24]
mechanical/enclosure-final-k/print-package/04-center-button.step
14.3 x 14.3 x 2.05 mm
