0x616c6f6e/esp32s31-mp3/mechanical/final-board-review/models3d/C0603_1_C9.step

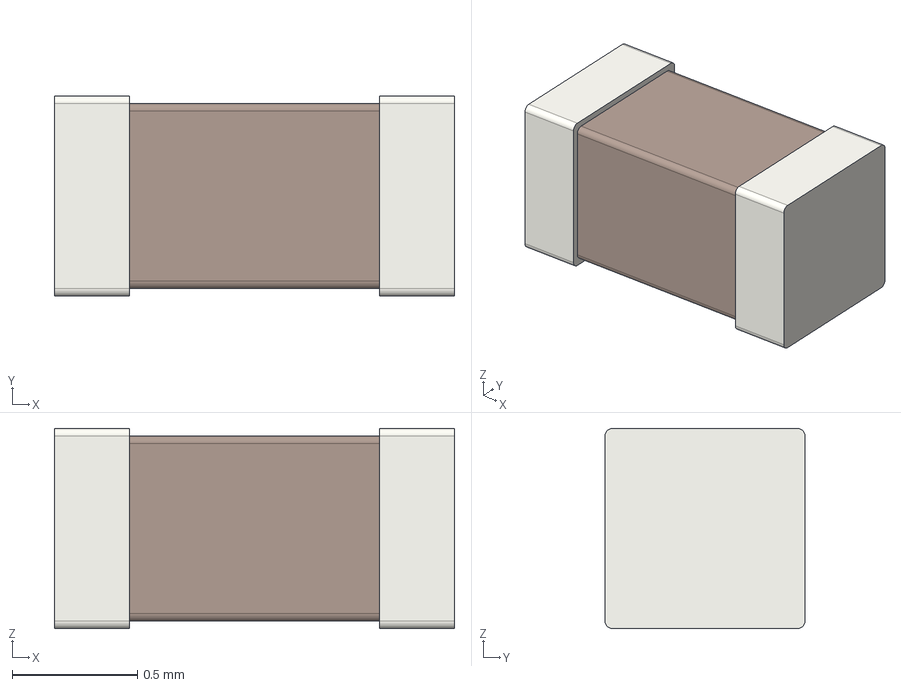
[picture p147: CAD file, 2026-09-21]
mechanical/final-board-review/models3d/C0603_1_C9.step
1.60 x 0.8 x 0.8 mm
