0x616c6f6e/esp32s31-mp3/hardware-q2-v2/models3d/TQFN-16_L3.0-W3.0-P0.50-BL-EP1.7.step

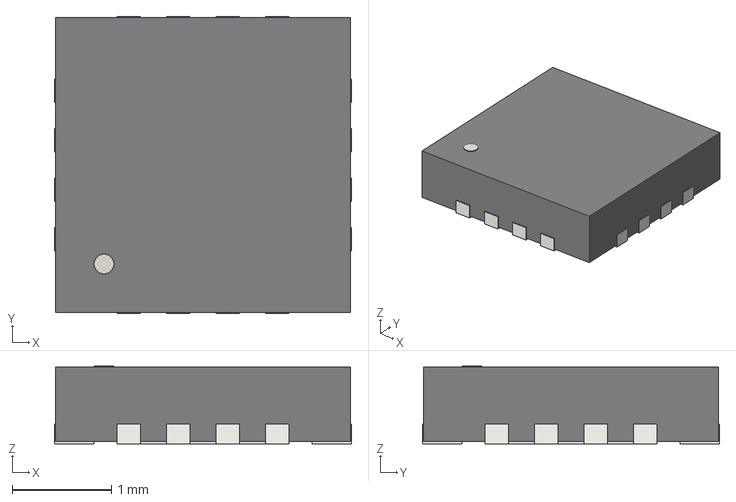
[picture p148: CAD file, 2026-09-21]
hardware-q2-v2/models3d/TQFN-16_L3.0-W3.0-P0.50-BL-EP1.7.step
3.00 x 3.00 x 0.785 mm
