0x616c6f6e/esp32s31-mp3/mechanical/enclosure-final-j/print-package/05-insert-fit-coupon-optional.step

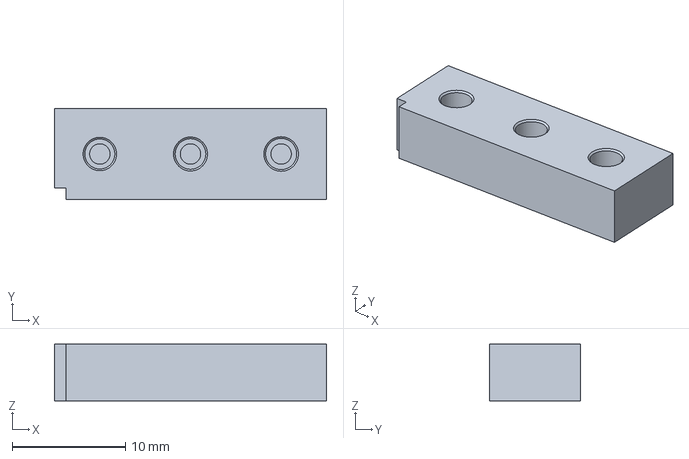
[picture p149: CAD file, 2026-09-24]
mechanical/enclosure-final-j/print-package/05-insert-fit-coupon-optional.step
24.0 x 8.00 x 5.00 mm
