0x616c6f6e/esp32s31-mp3/hardware-q2-v2/models3d/SOT-23-5_L3.0-W1.7-P0.95-LS2.8-BR_1.step

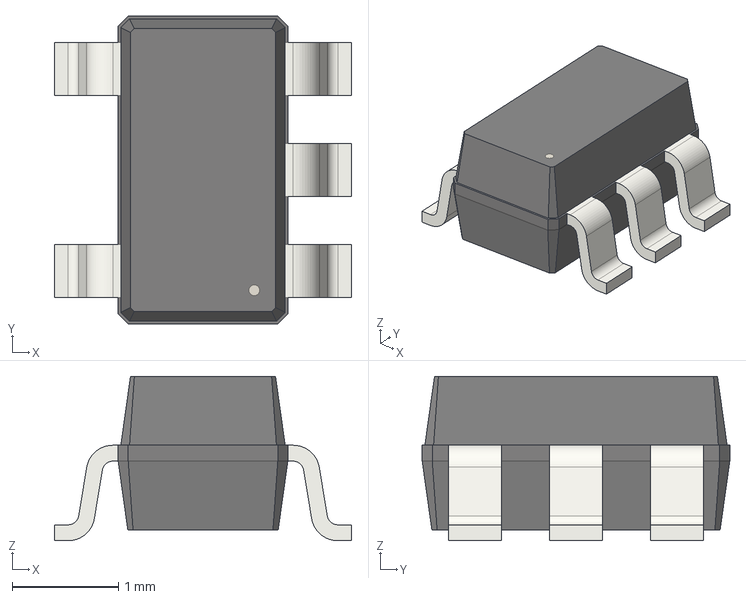
[picture p150: CAD file, 2026-09-21]
hardware-q2-v2/models3d/SOT-23-5_L3.0-W1.7-P0.95-LS2.8-BR_1.step
2.80 x 2.90 x 1.55 mm
