0x616c6f6e/esp32s31-mp3/mechanical/enclosure-final-l/prototype-parts-not-released/01-housing.step

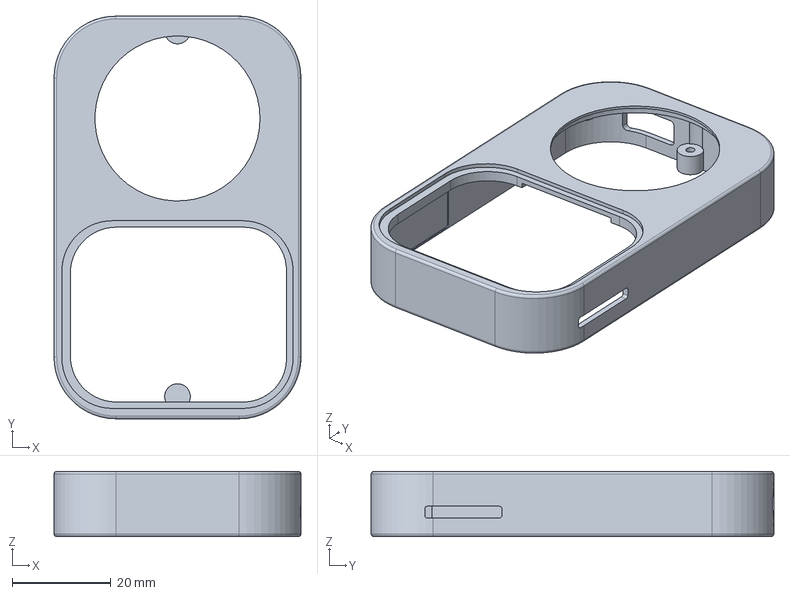
[picture p151: CAD file, 2026-09-24]
mechanical/enclosure-final-l/prototype-parts-not-released/01-housing.step
50.0 x 81.5 x 13.2 mm
