0x616c6f6e/esp32s31-mp3/mechanical/enclosure-q2-e/exports/q2-e-rear-cover.step

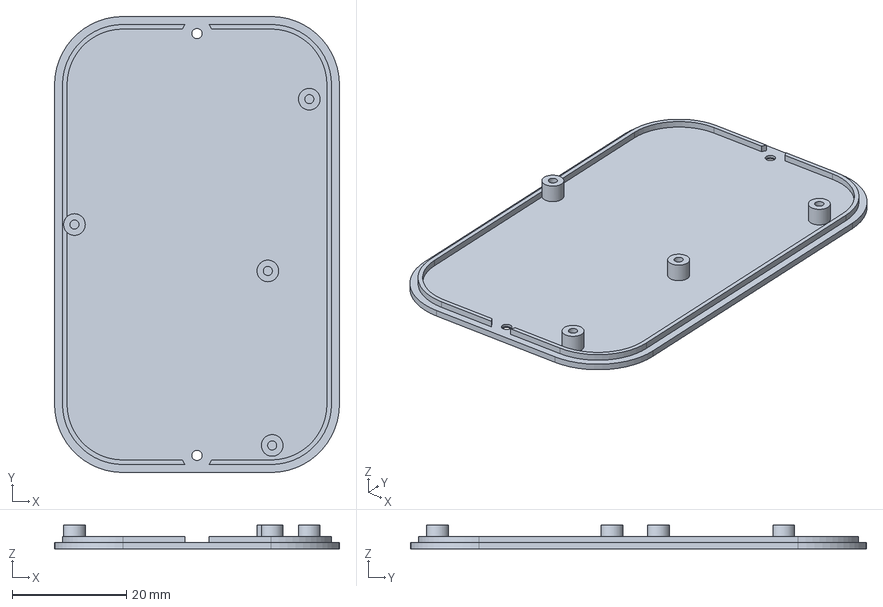
[picture p152: CAD file, 2026-09-21]
mechanical/enclosure-q2-e/exports/q2-e-rear-cover.step
50.0 x 80.0 x 4.20 mm
